upnalab/usarrayheightmod/Paper Photos/All Photos/Array/Foto1.png

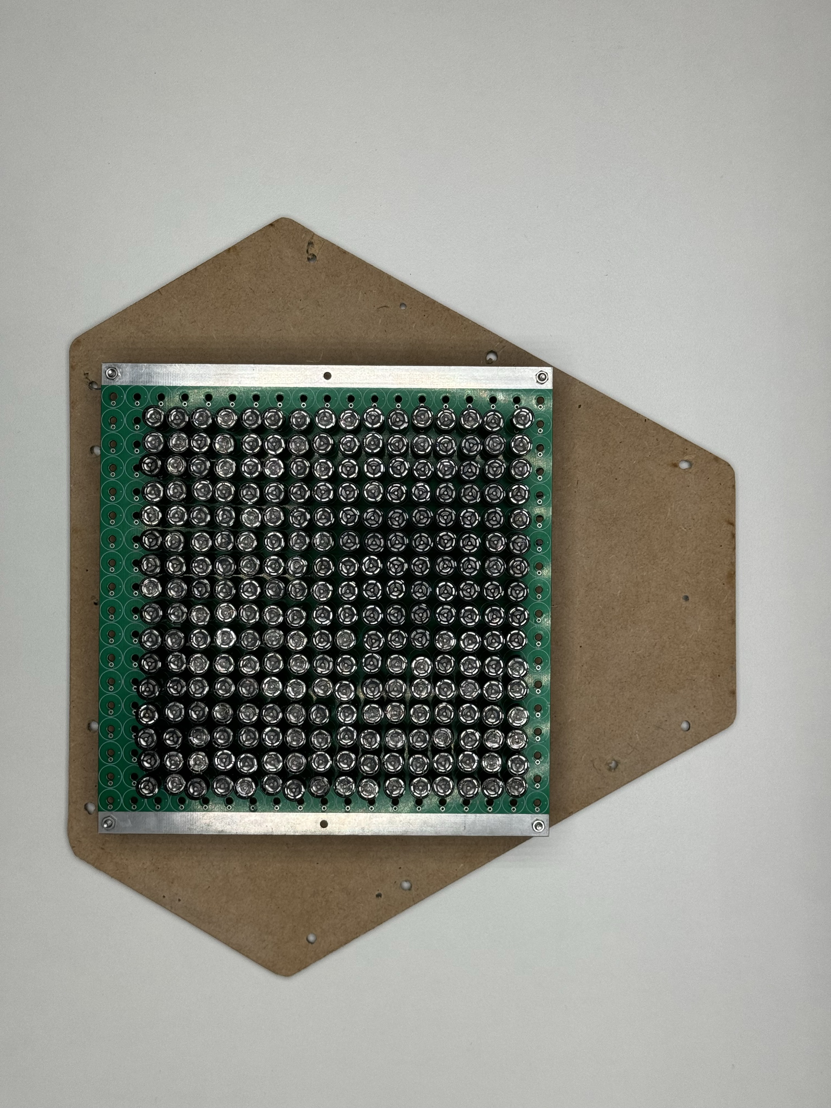
Paper Photos/All Photos/Array/Foto1.png
