upnalab/usarrayheightmod/Paper Photos/All Photos/Array/Foto2.png

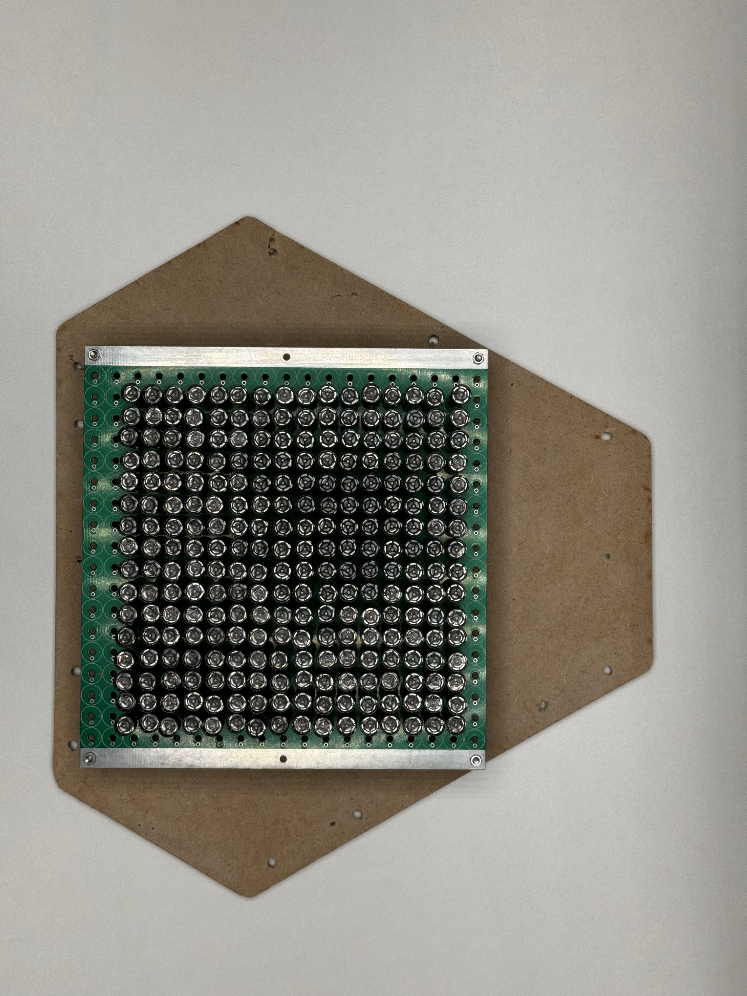
Paper Photos/All Photos/Array/Foto2.png
