upnalab/usarrayheightmod/Paper Photos/All Photos/Array/Foto3.png

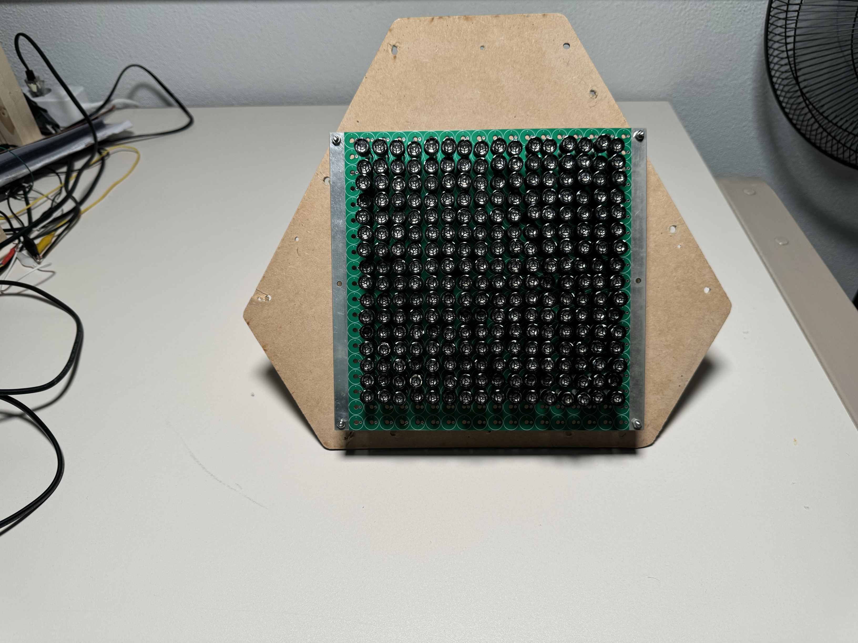
Paper Photos/All Photos/Array/Foto3.png
