upnalab/usarrayheightmod/Paper Photos/All Photos/Array/Foto4.png

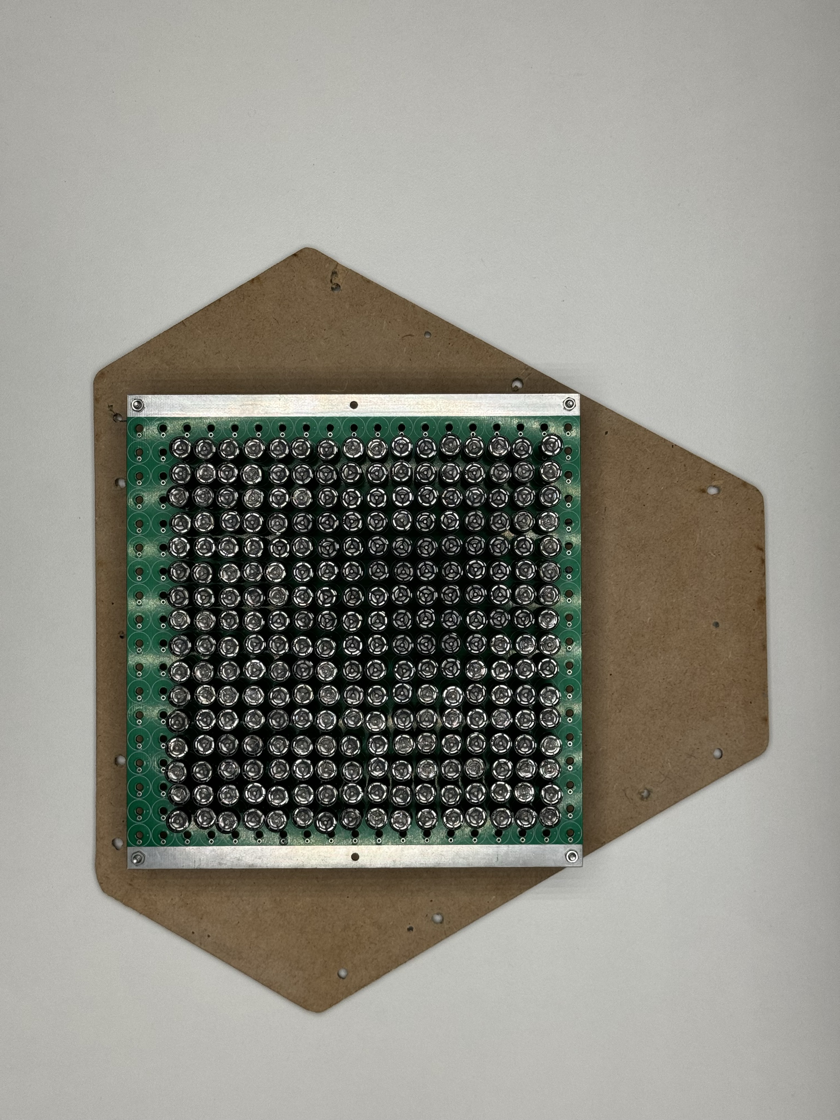
Paper Photos/All Photos/Array/Foto4.png
