upnalab/usarrayheightmod/Paper Photos/All Photos/Array/Foto5.png

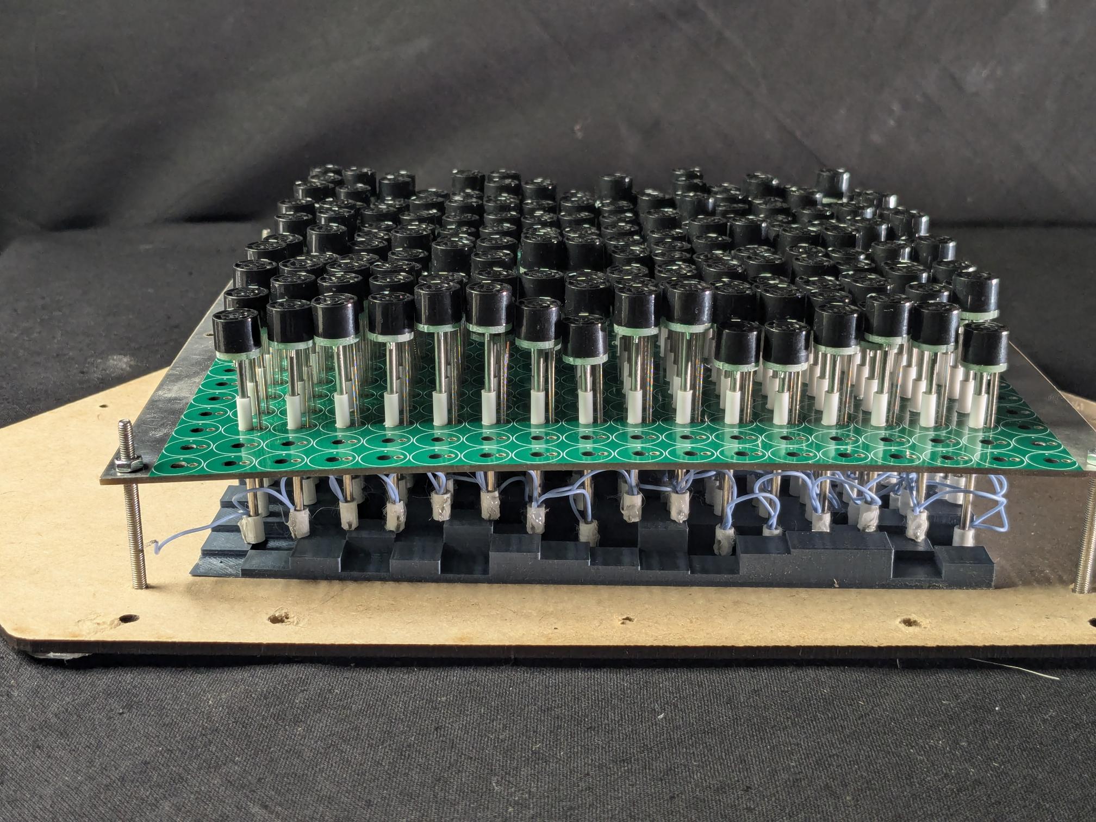
Paper Photos/All Photos/Array/Foto5.png
