upnalab/usarrayheightmod/Paper Photos/All Photos/Array/Foto6.png

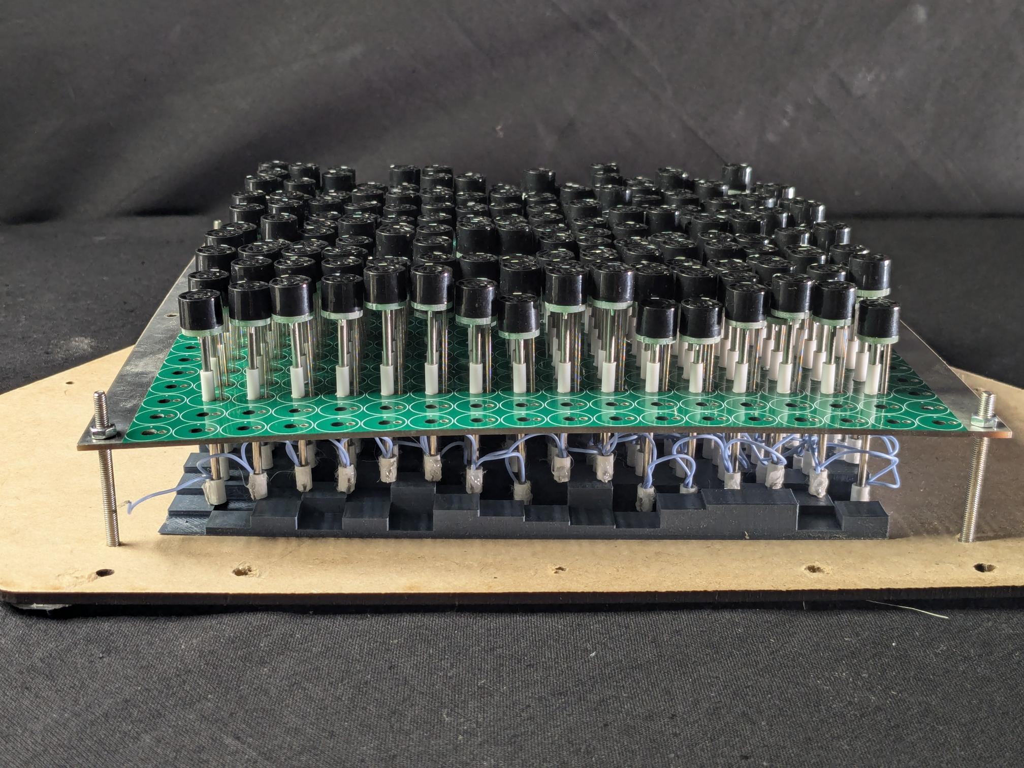
Paper Photos/All Photos/Array/Foto6.png
