upnalab/usarrayheightmod/Paper Photos/All Photos/Array/Foto7.png

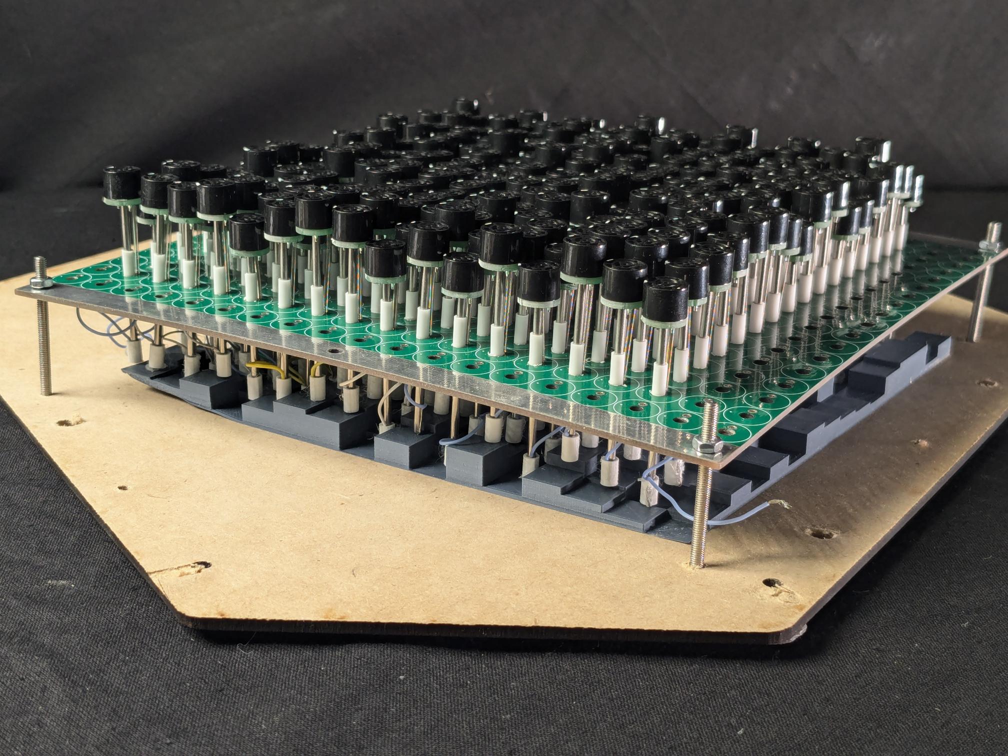
Paper Photos/All Photos/Array/Foto7.png
