upnalab/usarrayheightmod/Paper Photos/All Photos/Array/Foto8.png

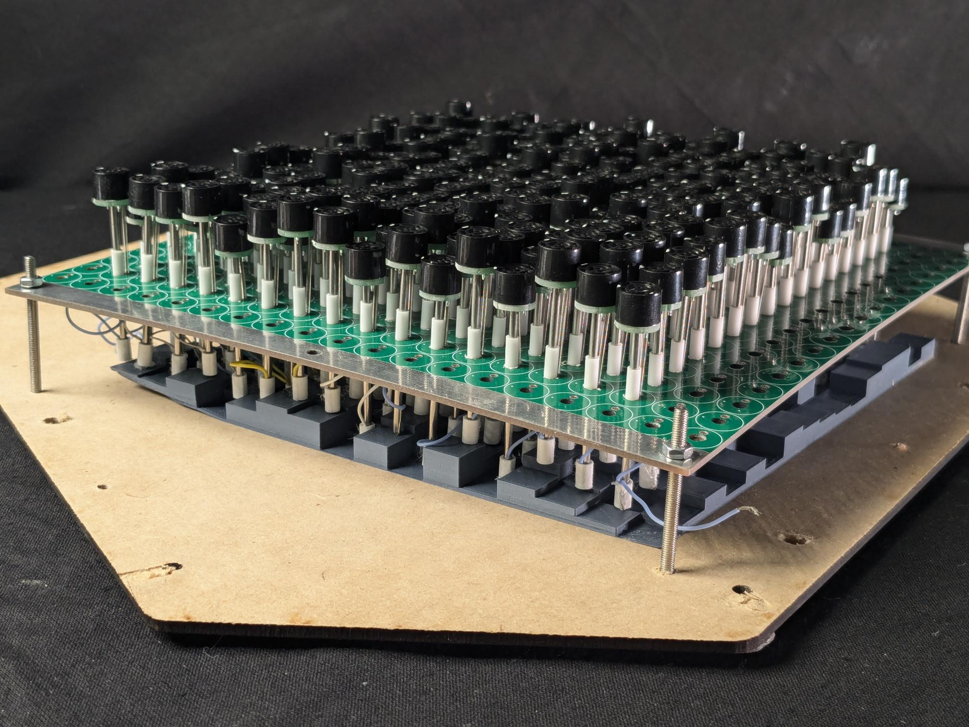
Paper Photos/All Photos/Array/Foto8.png
