upnalab/usarrayheightmod/Paper Photos/All Photos/Array/Foto9.png

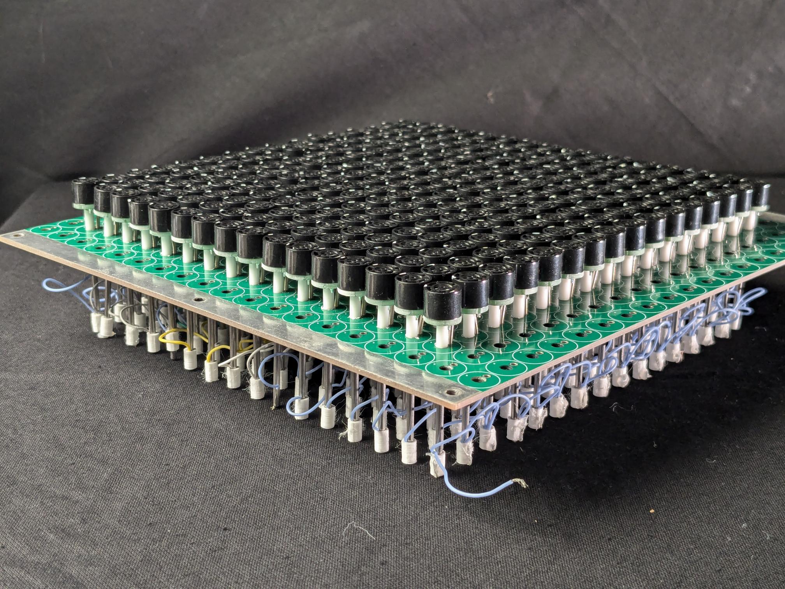
Paper Photos/All Photos/Array/Foto9.png
