upnalab/usarrayheightmod/Paper Photos/All Photos/Array/Foto10.png

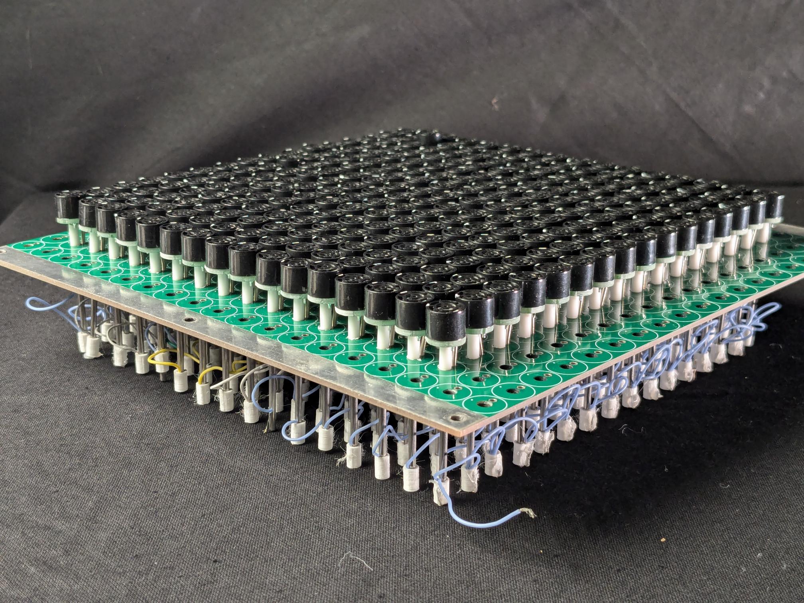
Paper Photos/All Photos/Array/Foto10.png
