upnalab/usarrayheightmod/Paper Photos/All Photos/Array/Foto11.png

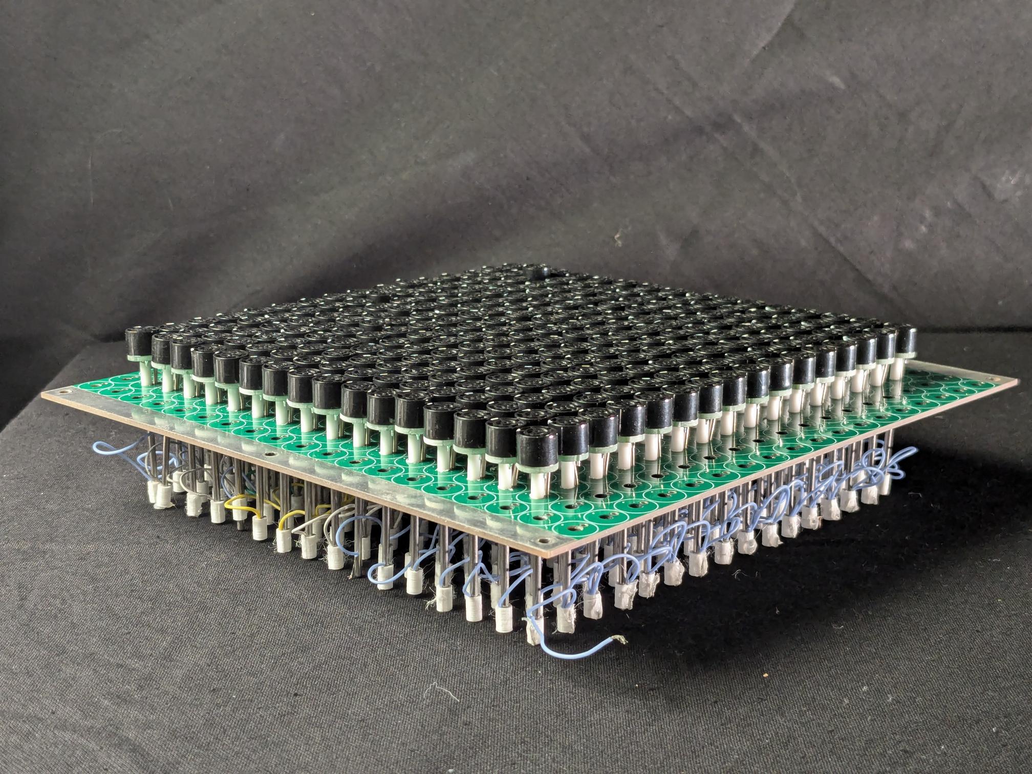
Paper Photos/All Photos/Array/Foto11.png
