upnalab/usarrayheightmod/Paper Photos/All Photos/Array/Foto12.png

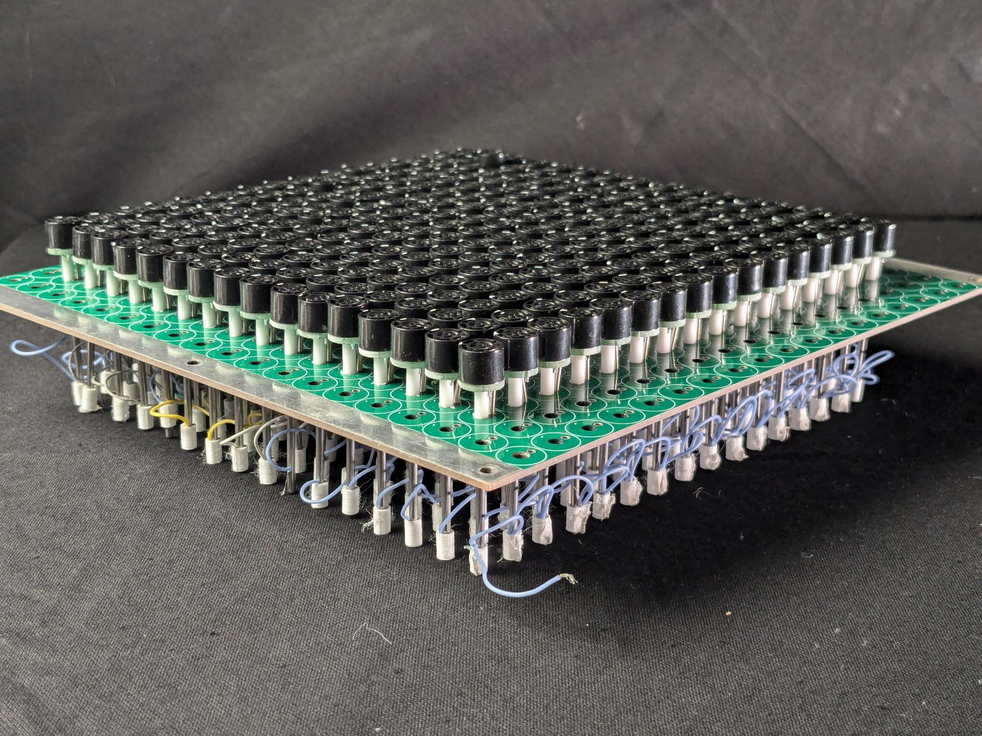
Paper Photos/All Photos/Array/Foto12.png
