upnalab/usarrayheightmod/Paper Photos/All Photos/Array/Foto13.png

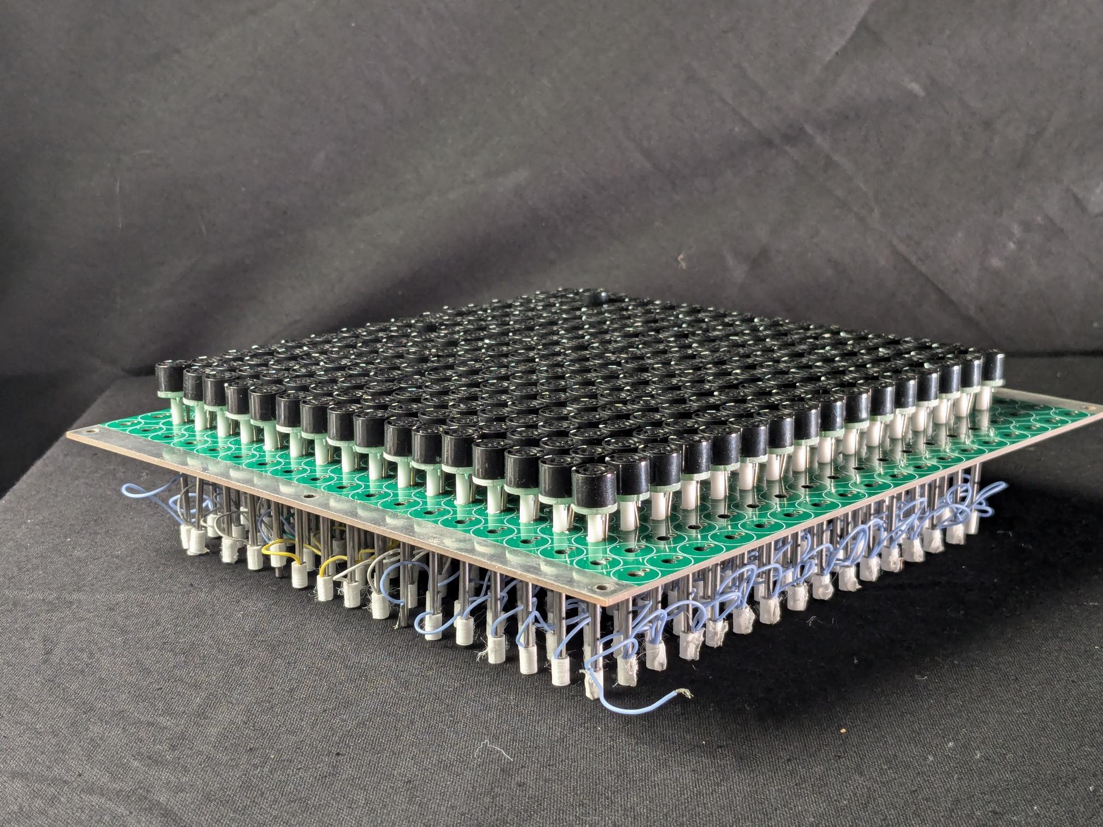
Paper Photos/All Photos/Array/Foto13.png
