upnalab/usarrayheightmod/Paper Photos/All Photos/Array/Foto18.png

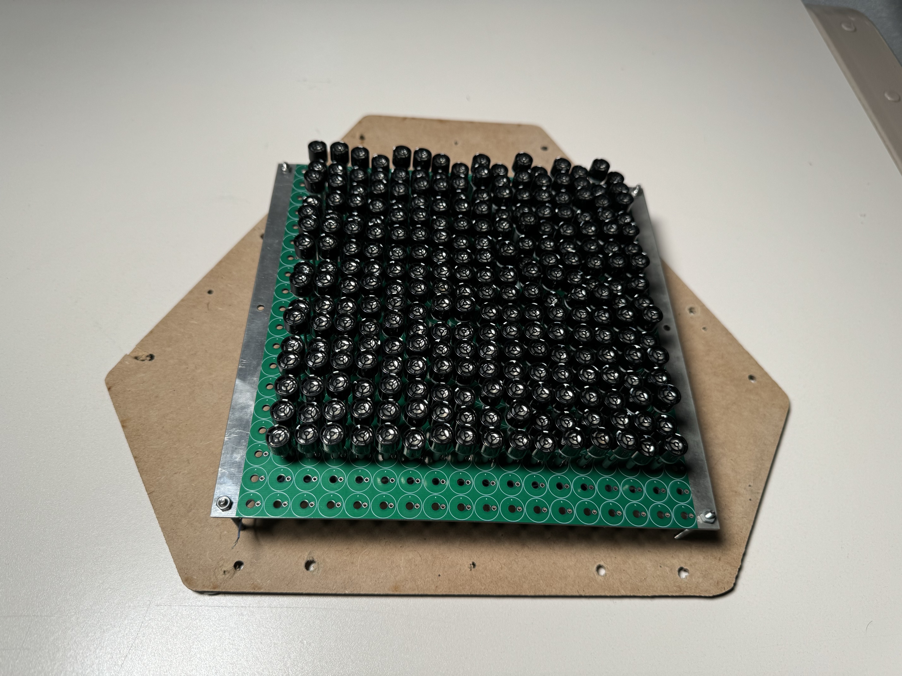
Paper Photos/All Photos/Array/Foto18.png
