upnalab/usarrayheightmod/Paper Photos/All Photos/Array/Foto19.png

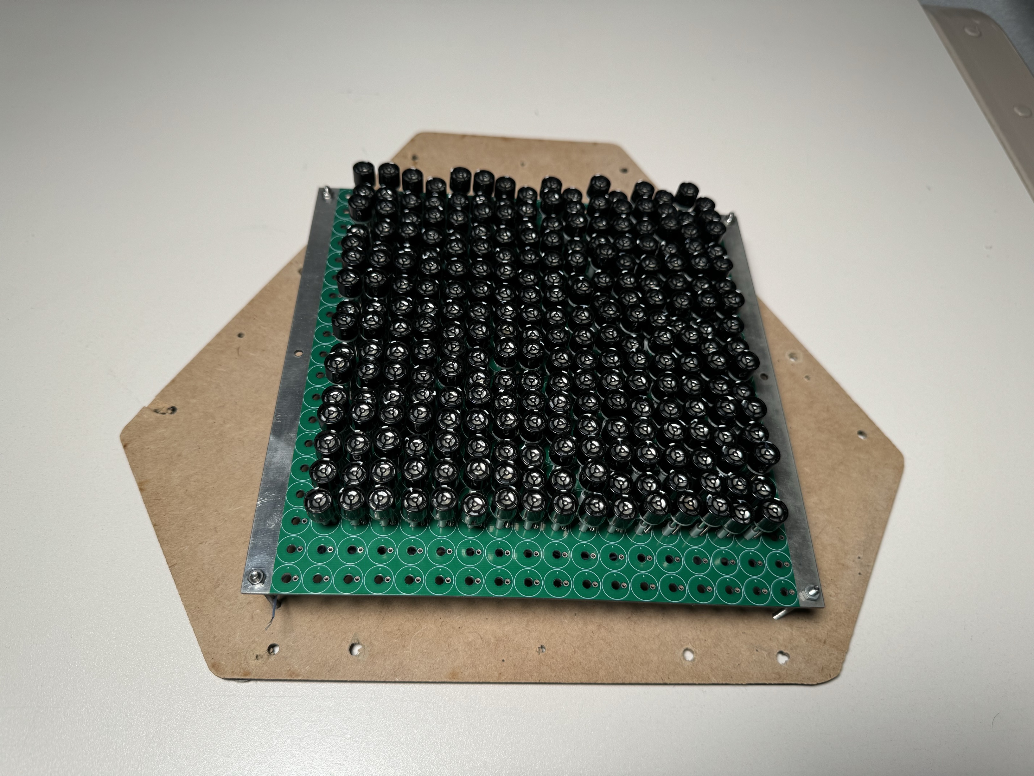
Paper Photos/All Photos/Array/Foto19.png
