upnalab/usarrayheightmod/Paper Photos/All Photos/Array/Foto20.png

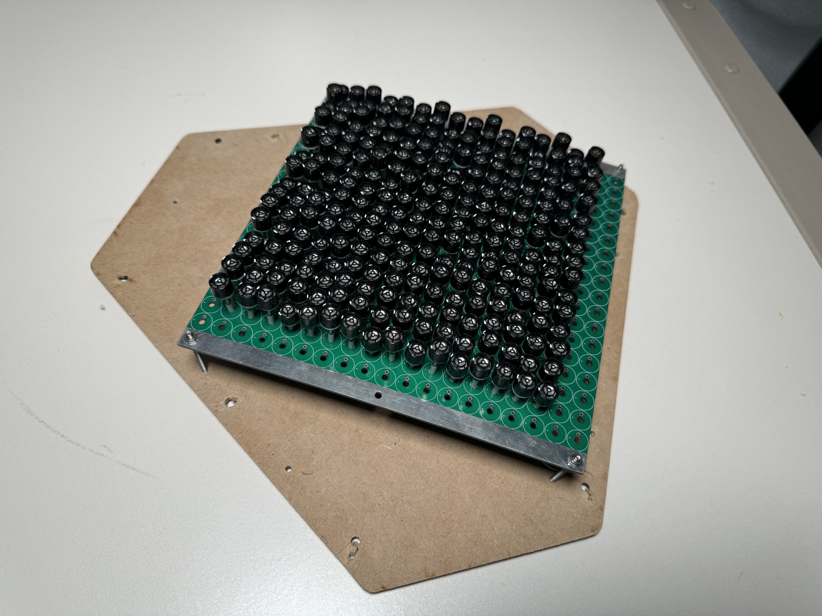
Paper Photos/All Photos/Array/Foto20.png
