upnalab/usarrayheightmod/Paper Photos/All Photos/Array/Foto24.png

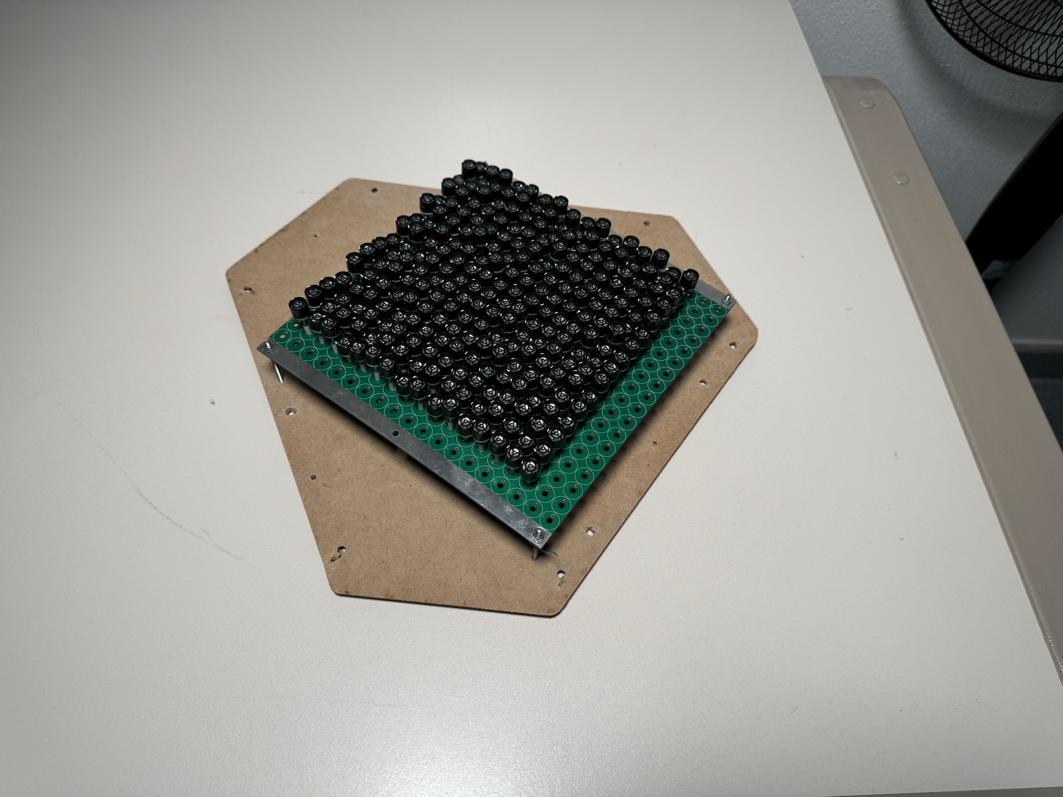
Paper Photos/All Photos/Array/Foto24.png
