upnalab/usarrayheightmod/Paper Photos/All Photos/Array/Foto25.png

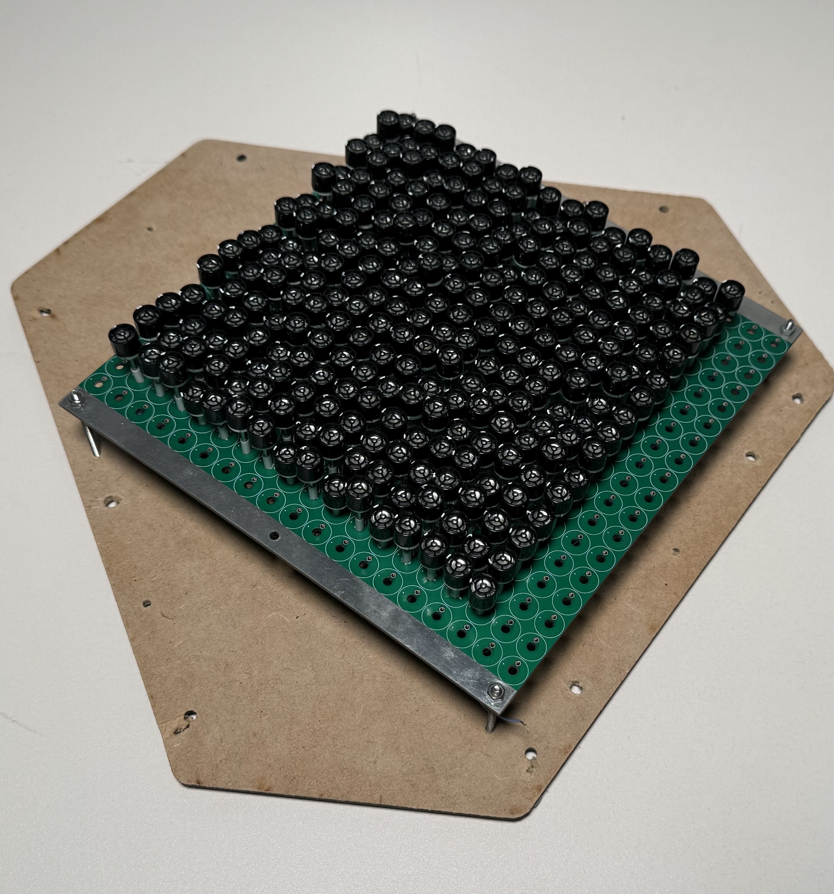
Paper Photos/All Photos/Array/Foto25.png
