upnalab/usarrayheightmod/Paper Photos/All Photos/Array/Foto27.png

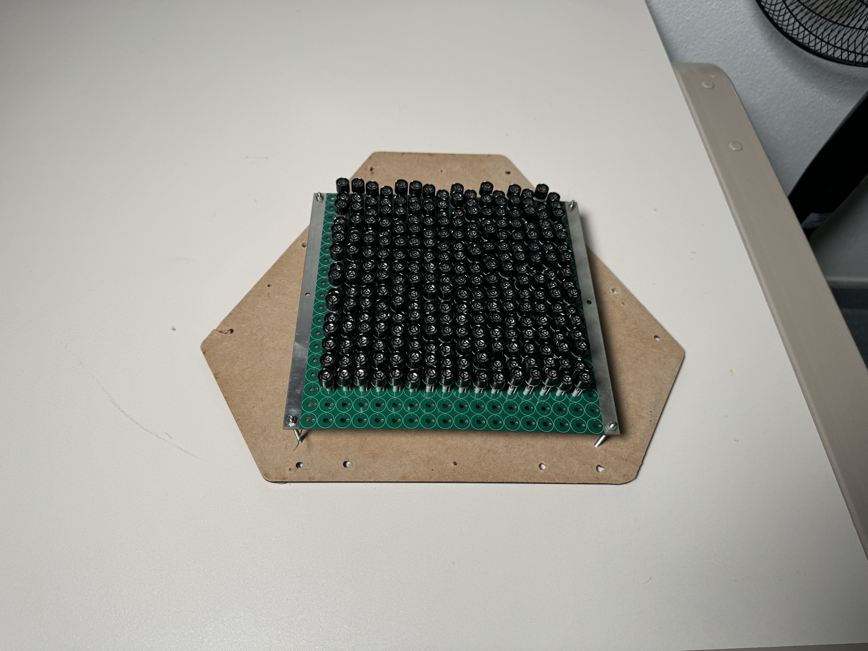
Paper Photos/All Photos/Array/Foto27.png
