upnalab/usarrayheightmod/Paper Photos/All Photos/Array/Foto29.png

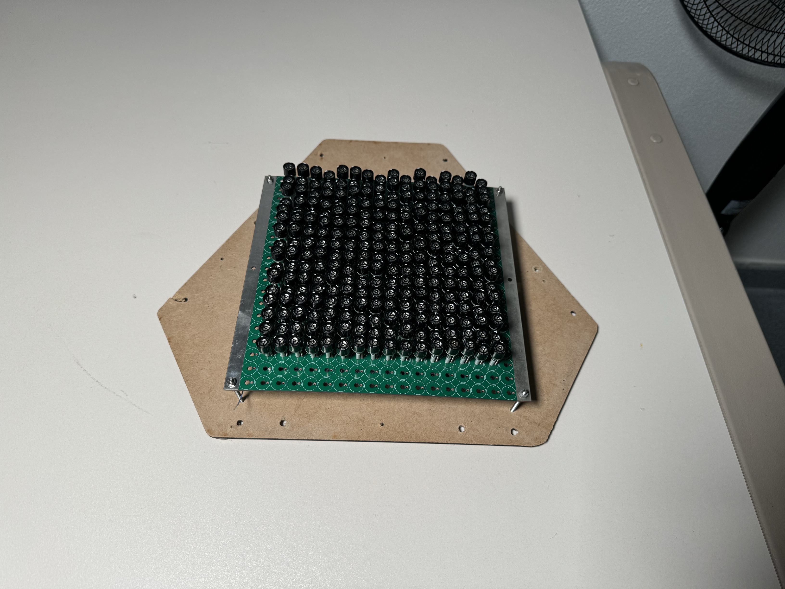
Paper Photos/All Photos/Array/Foto29.png
