upnalab/usarrayheightmod/Paper Photos/All Photos/Array/Foto30.png

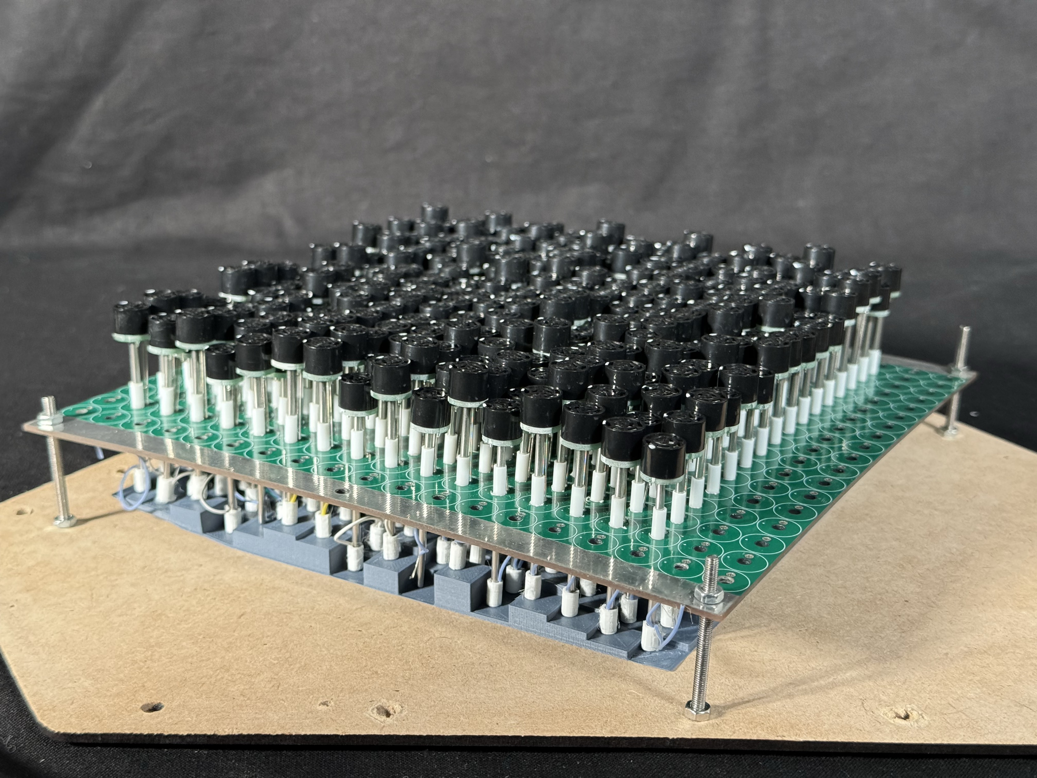
Paper Photos/All Photos/Array/Foto30.png
