upnalab/usarrayheightmod/Paper Photos/All Photos/Array/Foto31.png

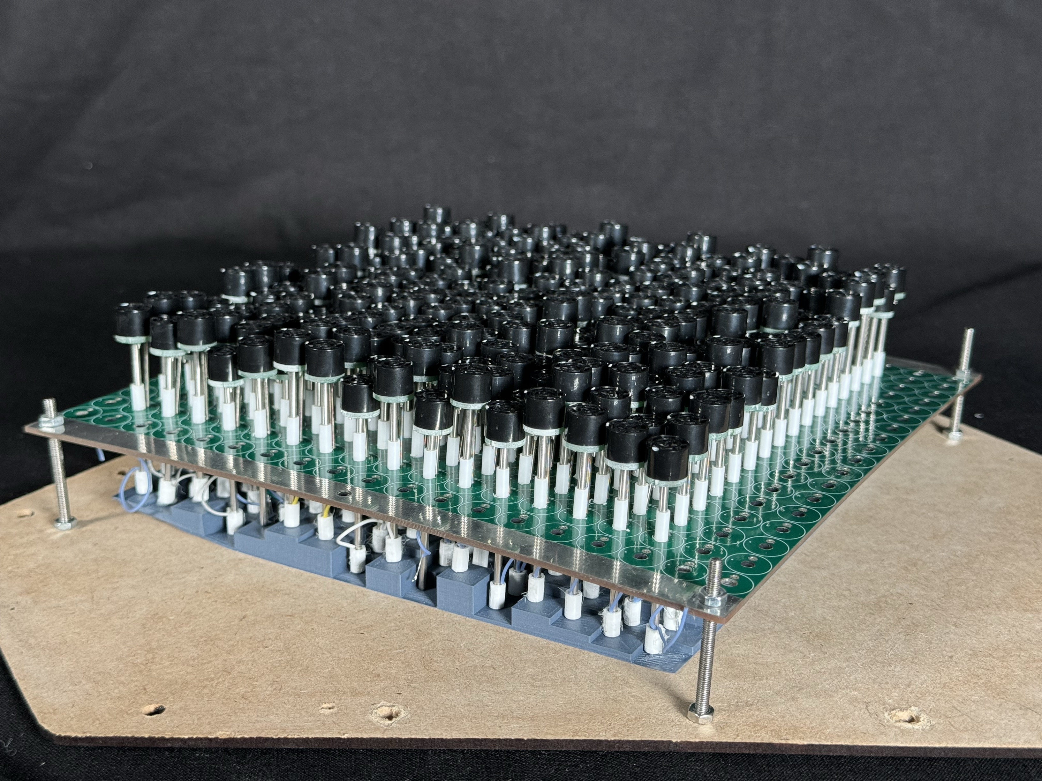
Paper Photos/All Photos/Array/Foto31.png
