upnalab/usarrayheightmod/Paper Photos/All Photos/Array/Foto33.png

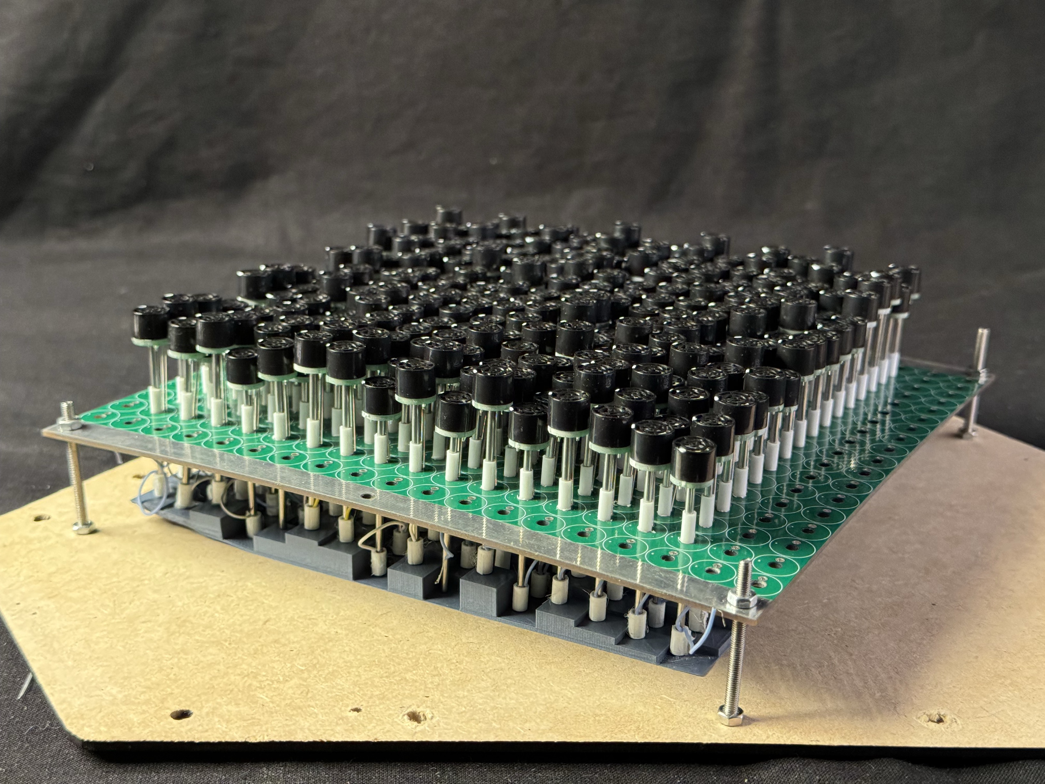
Paper Photos/All Photos/Array/Foto33.png
