upnalab/usarrayheightmod/Paper Photos/All Photos/Array/Foto35.png

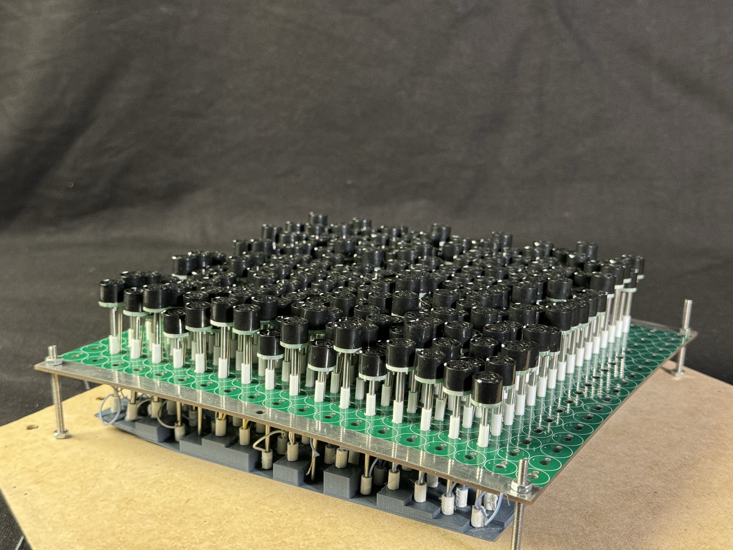
Paper Photos/All Photos/Array/Foto35.png
