upnalab/usarrayheightmod/Paper Photos/All Photos/Array/Foto37.png

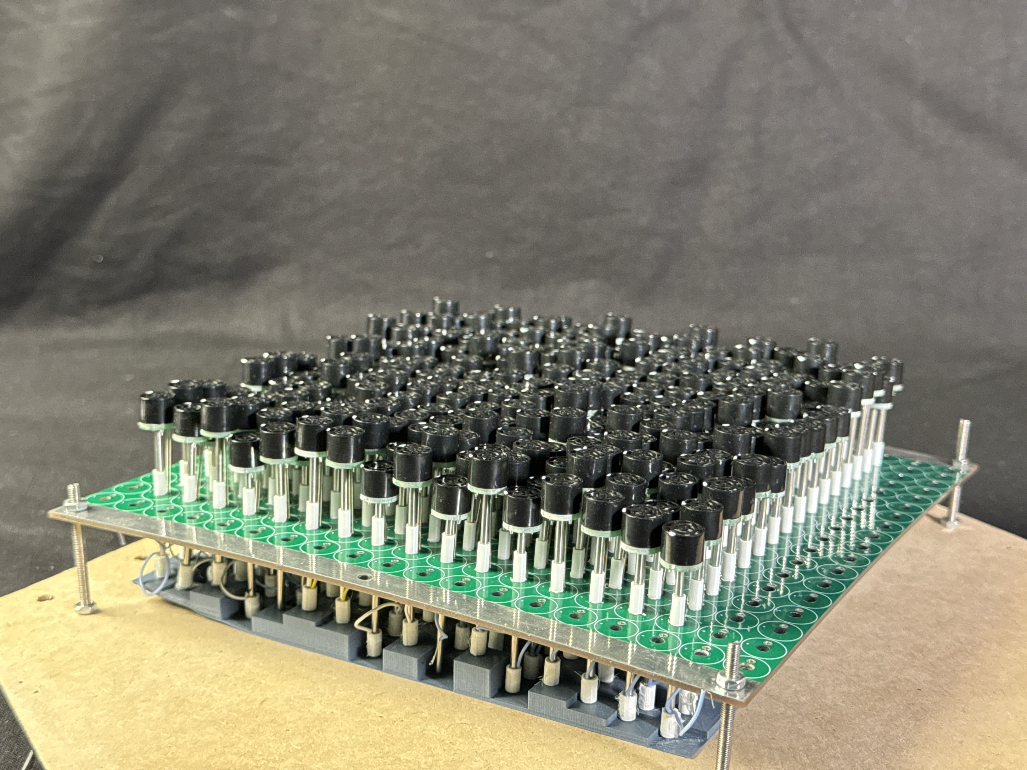
Paper Photos/All Photos/Array/Foto37.png
