upnalab/usarrayheightmod/Paper Photos/All Photos/Array/Foto41.png

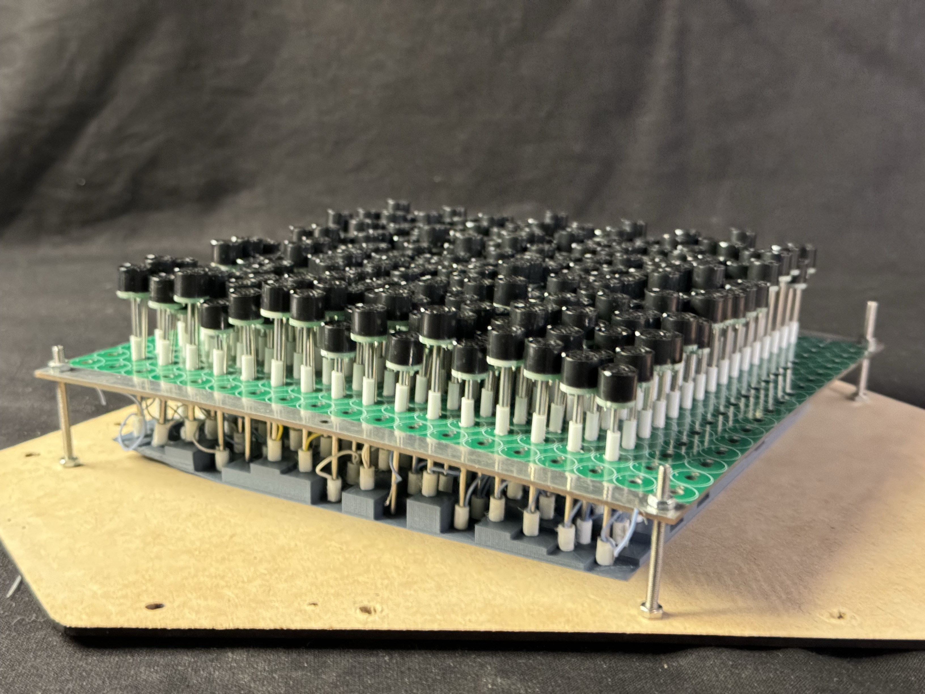
Paper Photos/All Photos/Array/Foto41.png
