upnalab/usarrayheightmod/Paper Photos/All Photos/Array/Foto42.png

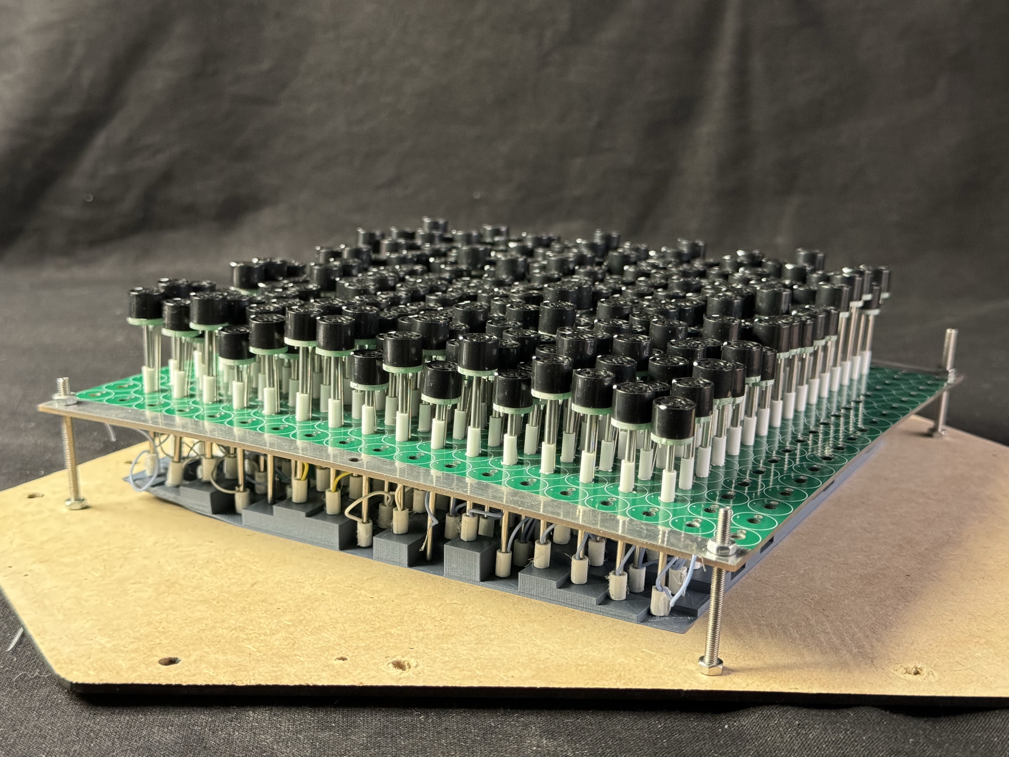
Paper Photos/All Photos/Array/Foto42.png
