upnalab/usarrayheightmod/Paper Photos/All Photos/Array/Foto43.png

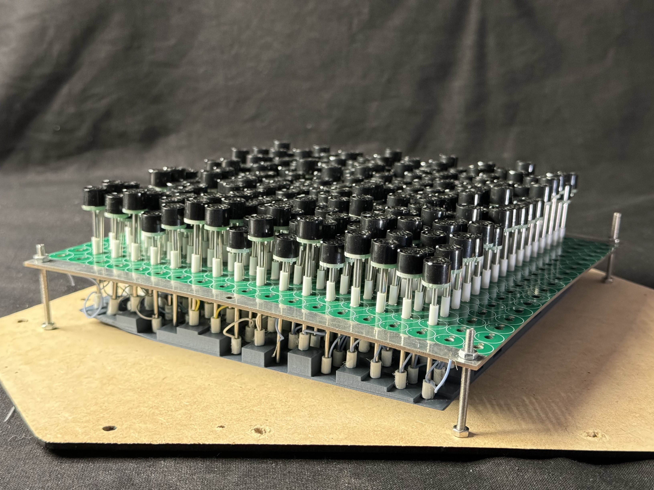
Paper Photos/All Photos/Array/Foto43.png
