upnalab/usarrayheightmod/Paper Photos/All Photos/Array/Foto45.png

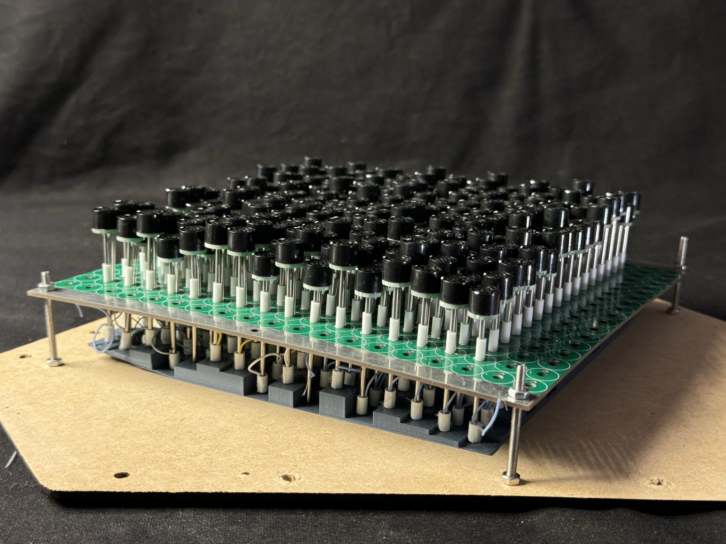
Paper Photos/All Photos/Array/Foto45.png
