upnalab/usarrayheightmod/Paper Photos/All Photos/Array/Foto47.png

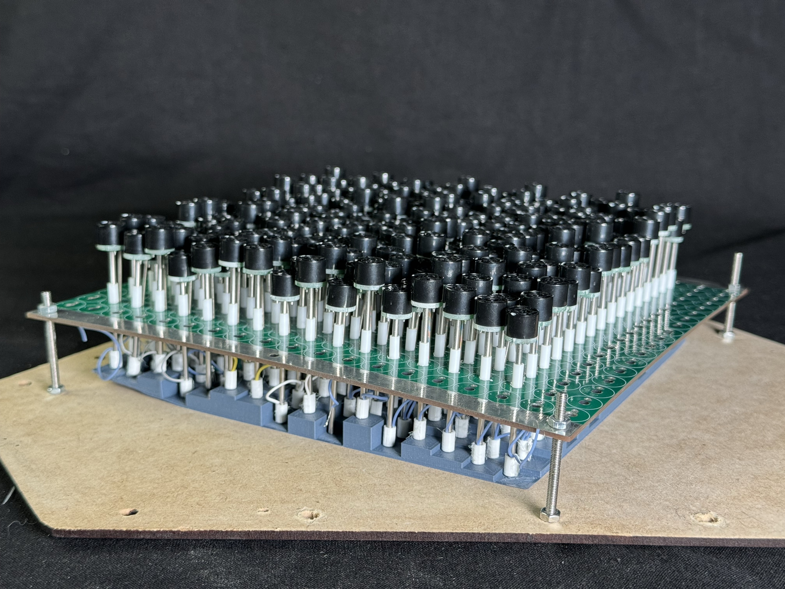
Paper Photos/All Photos/Array/Foto47.png
