upnalab/usarrayheightmod/Paper Photos/All Photos/Array/Foto49.png

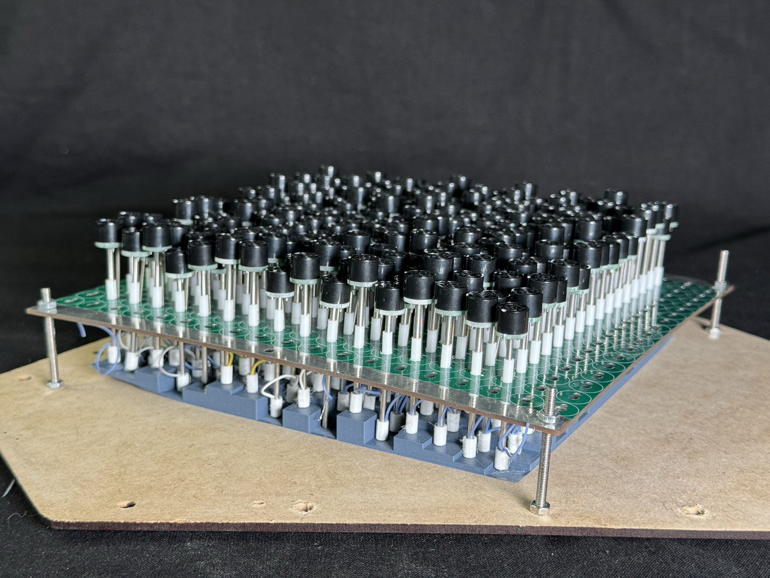
Paper Photos/All Photos/Array/Foto49.png
