upnalab/usarrayheightmod/Paper Photos/All Photos/Array/Foto51.png

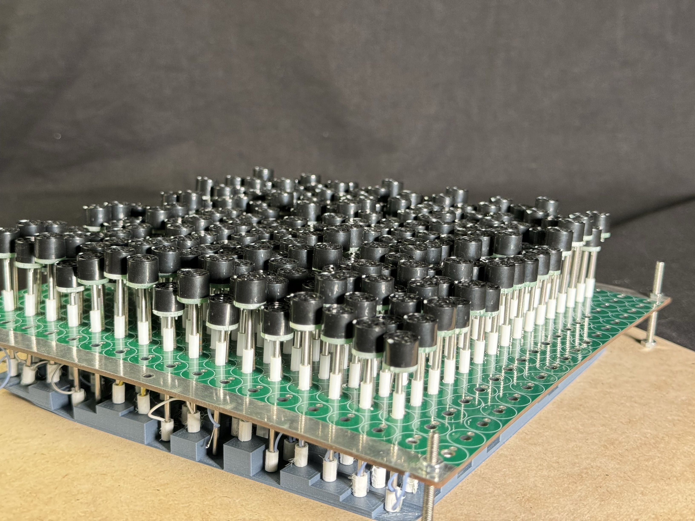
Paper Photos/All Photos/Array/Foto51.png
