upnalab/usarrayheightmod/Paper Photos/All Photos/Array/Foto52.png

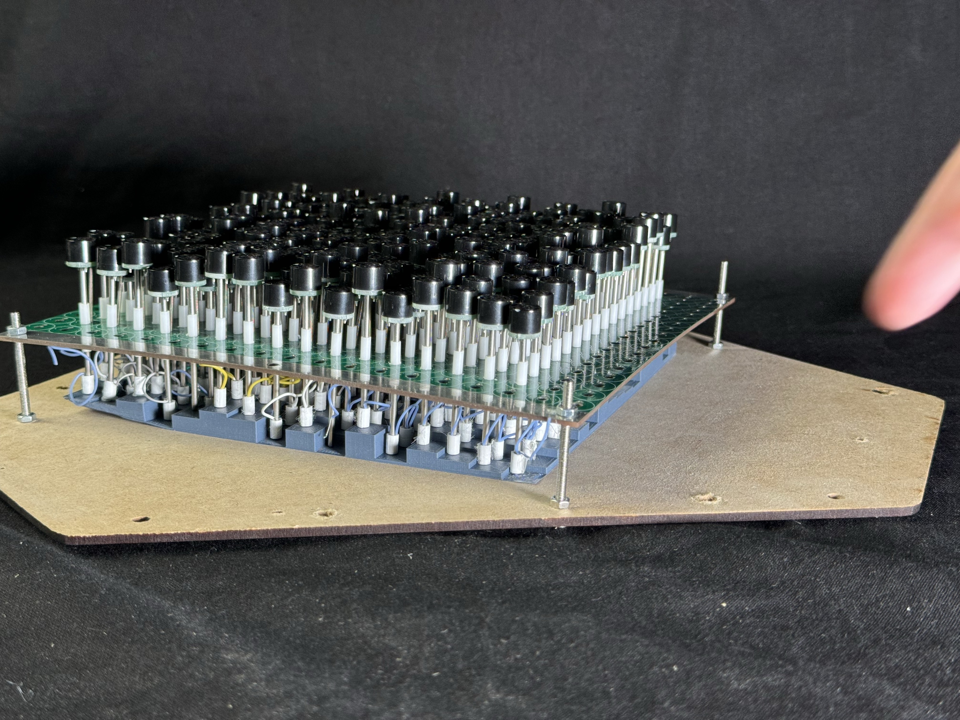
Paper Photos/All Photos/Array/Foto52.png
