upnalab/usarrayheightmod/Paper Photos/All Photos/Array/Foto53.png

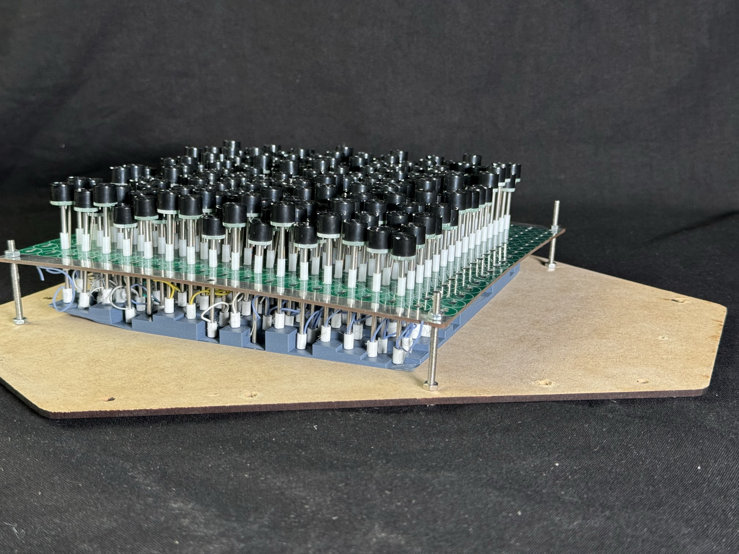
Paper Photos/All Photos/Array/Foto53.png
