upnalab/usarrayheightmod/Paper Photos/All Photos/Array/Foto54.png

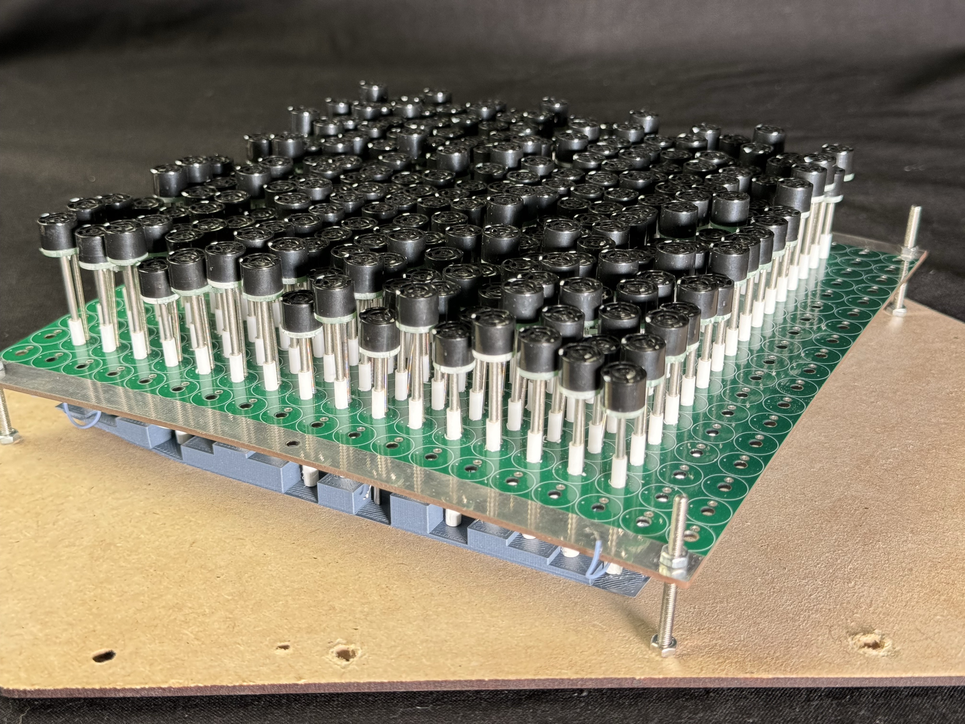
Paper Photos/All Photos/Array/Foto54.png
