upnalab/usarrayheightmod/Paper Photos/All Photos/Array/Foto57.png

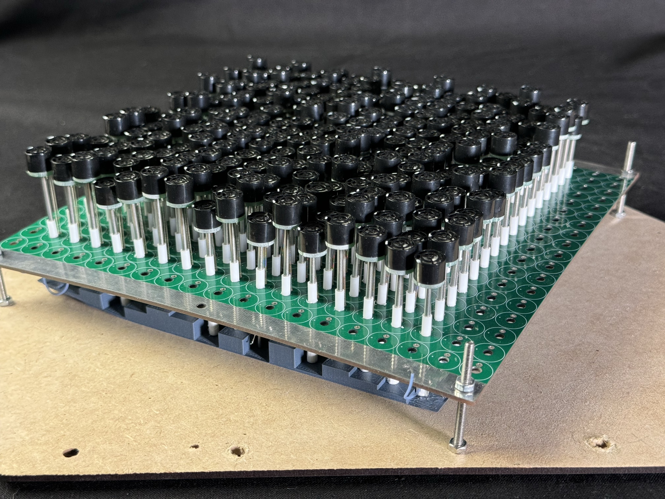
Paper Photos/All Photos/Array/Foto57.png
