upnalab/usarrayheightmod/Paper Photos/All Photos/Array/Foto58.png

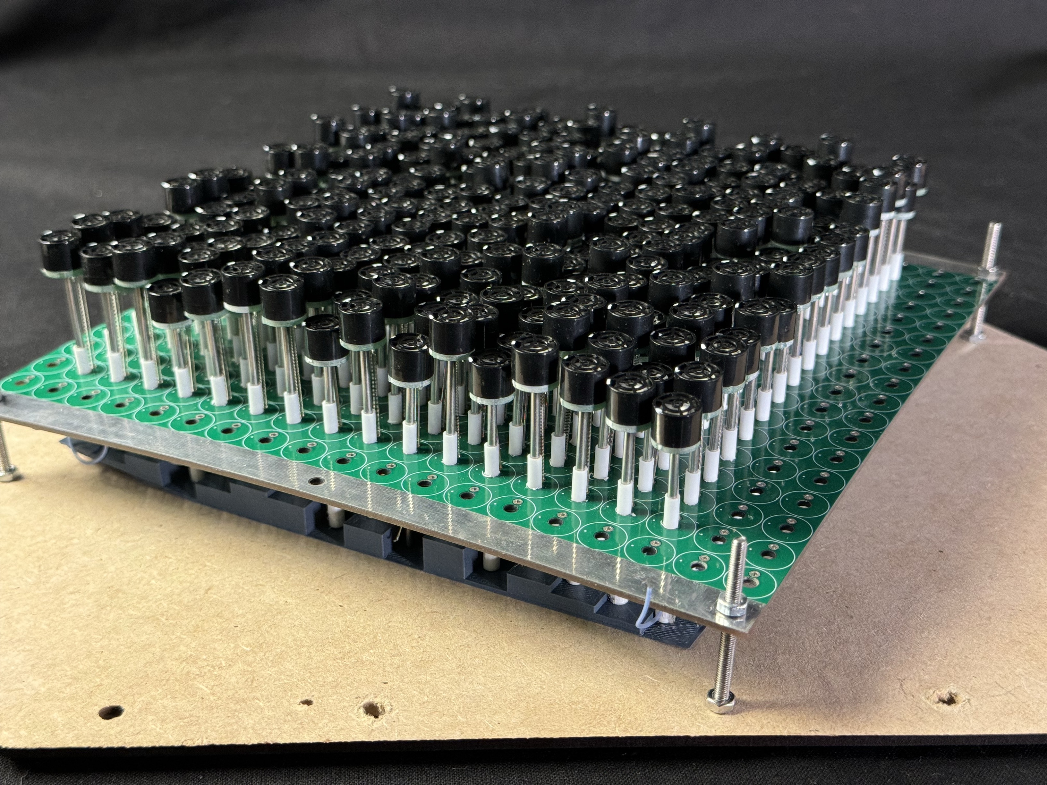
Paper Photos/All Photos/Array/Foto58.png
