upnalab/usarrayheightmod/Paper Photos/All Photos/Array/Foto60.png

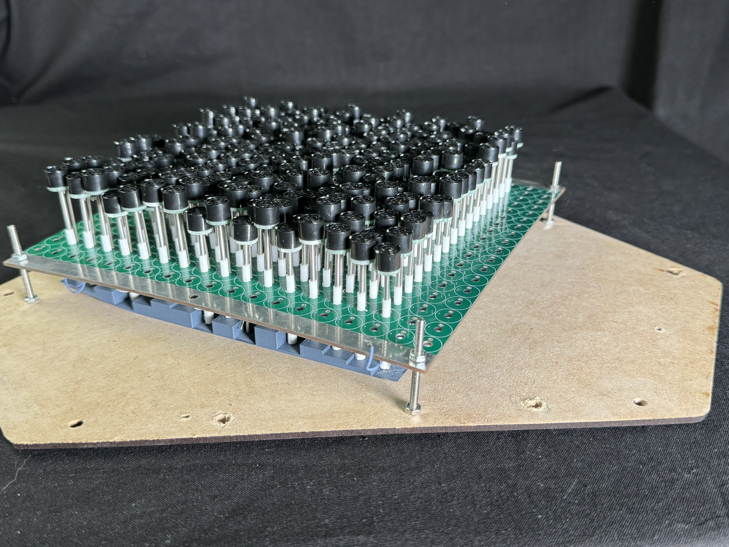
Paper Photos/All Photos/Array/Foto60.png
