upnalab/usarrayheightmod/Paper Photos/All Photos/Array/Foto63.png

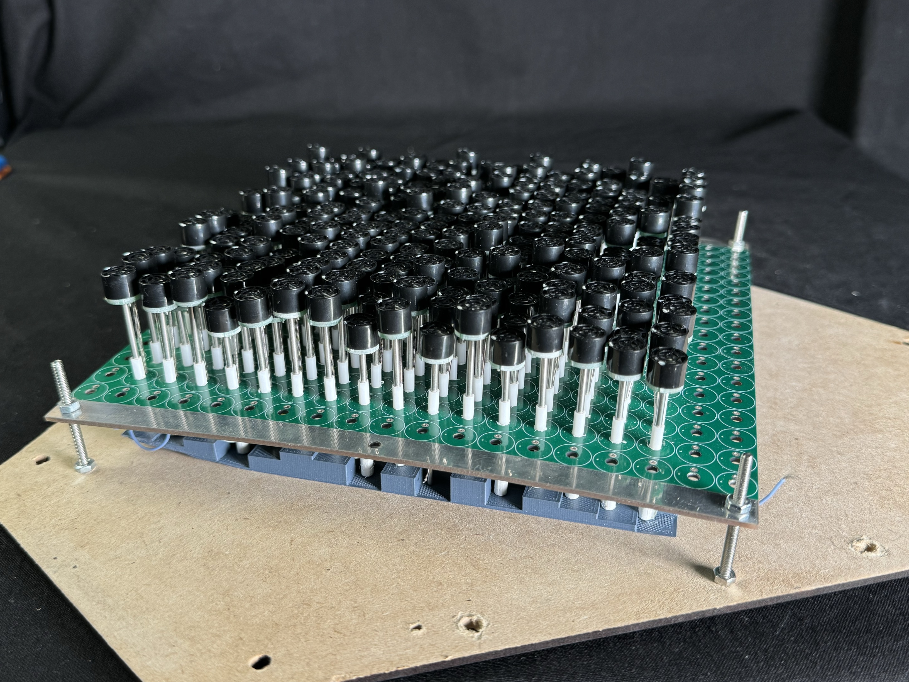
Paper Photos/All Photos/Array/Foto63.png
