upnalab/usarrayheightmod/Paper Photos/All Photos/Array/Foto64.png

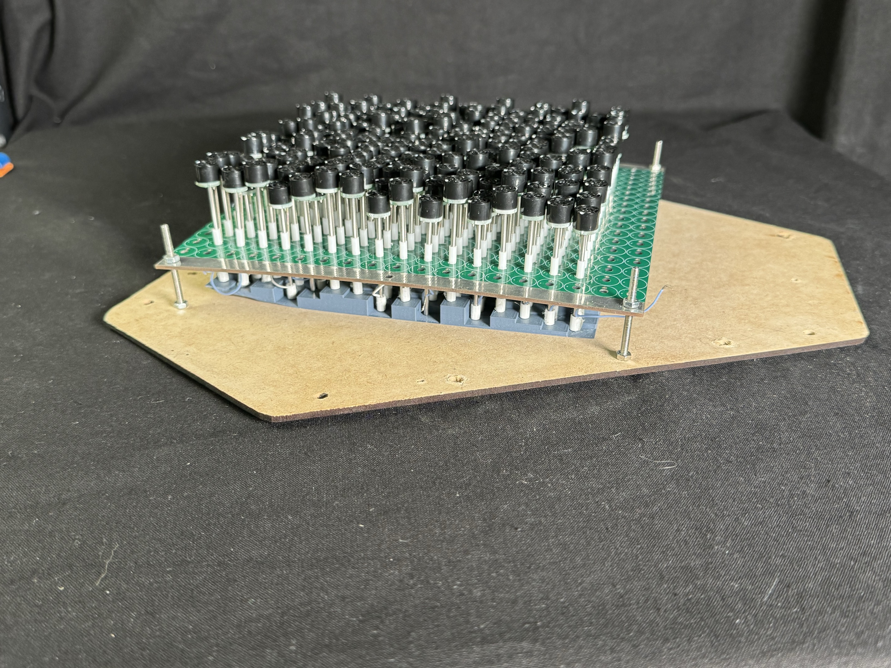
Paper Photos/All Photos/Array/Foto64.png
