upnalab/usarrayheightmod/Paper Photos/All Photos/Array/Foto67.png

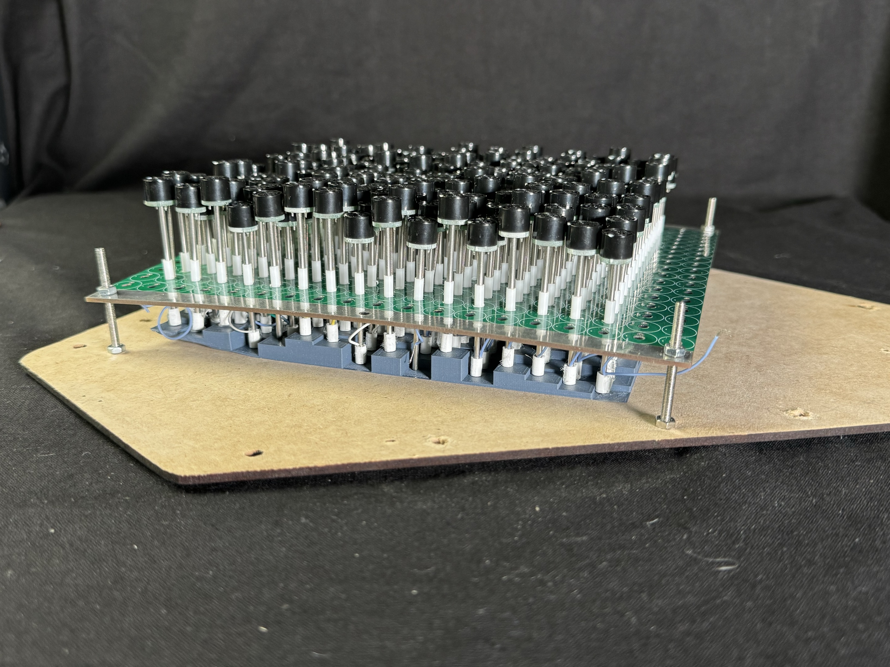
Paper Photos/All Photos/Array/Foto67.png
