upnalab/usarrayheightmod/Paper Photos/All Photos/Array/Foto68.png

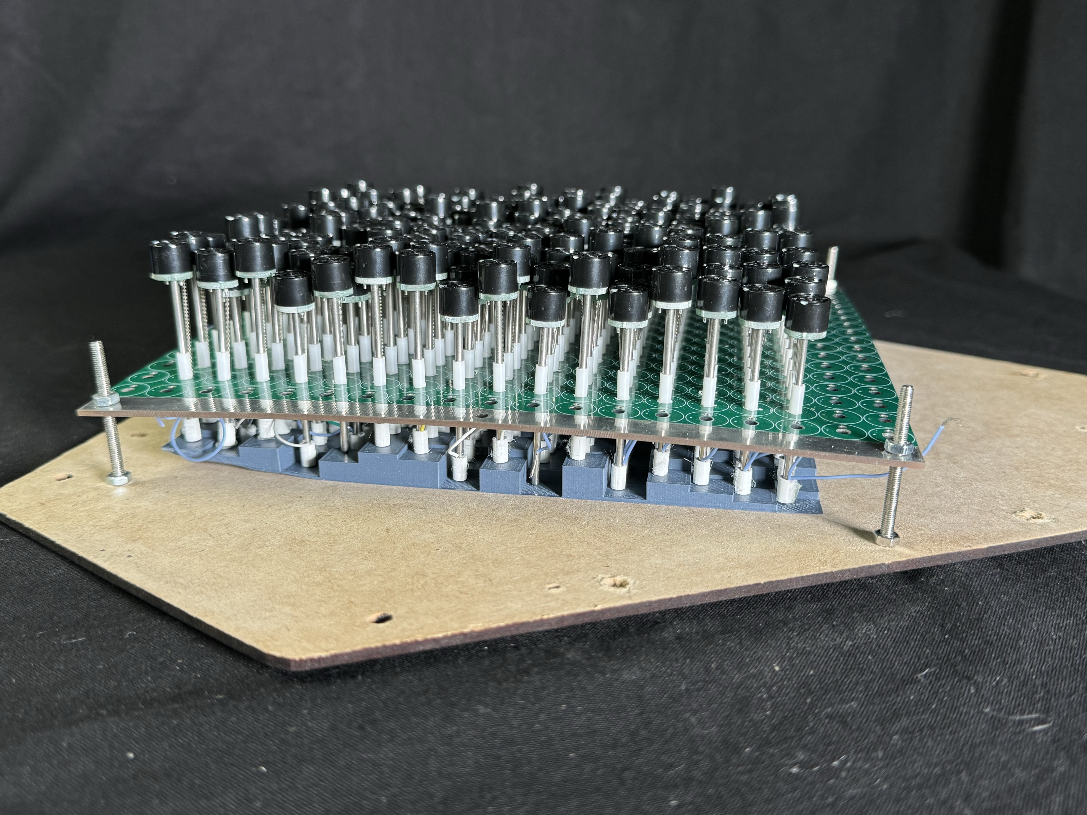
Paper Photos/All Photos/Array/Foto68.png
