upnalab/usarrayheightmod/Paper Photos/All Photos/Metasurface/Foto1.png

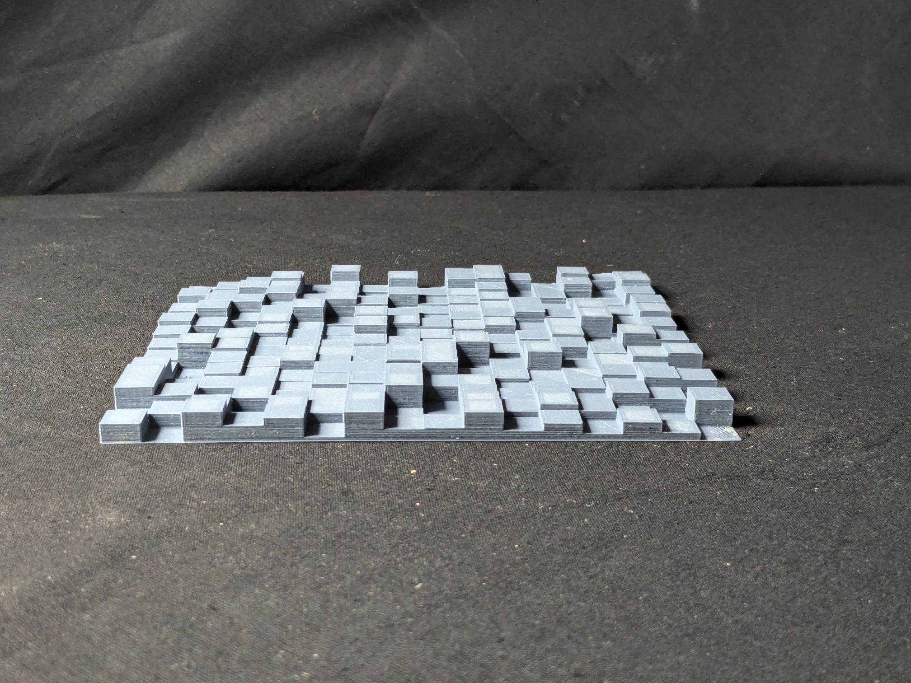
Paper Photos/All Photos/Metasurface/Foto1.png
