upnalab/usarrayheightmod/Paper Photos/All Photos/Metasurface/Foto3.png

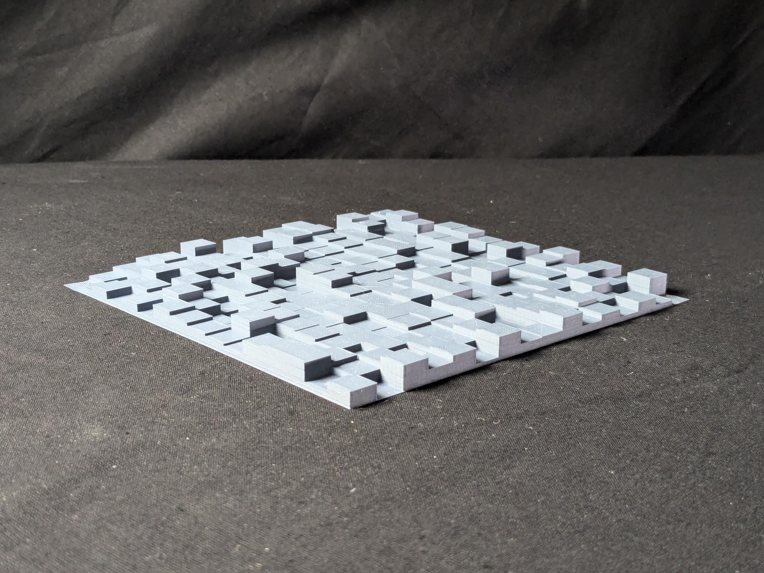
Paper Photos/All Photos/Metasurface/Foto3.png
