upnalab/usarrayheightmod/Paper Photos/All Photos/Scan_SetUp/_DSC2678.JPG

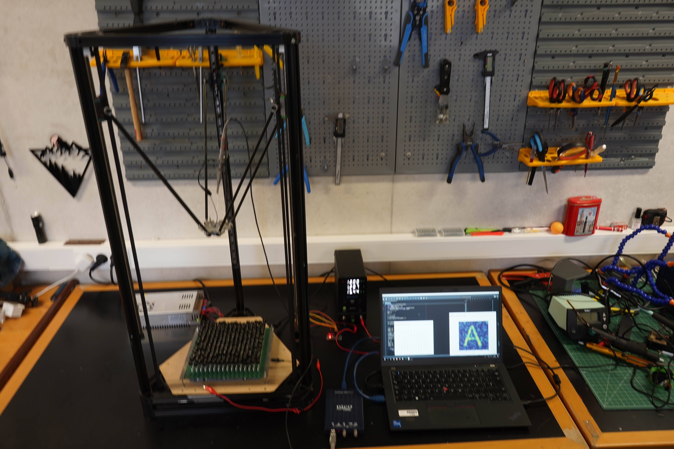
Paper Photos/All Photos/Scan_SetUp/_DSC2678.JPG
