upnalab/usarrayheightmod/Paper Photos/All Photos/Scan_SetUp/_DSC2679.JPG

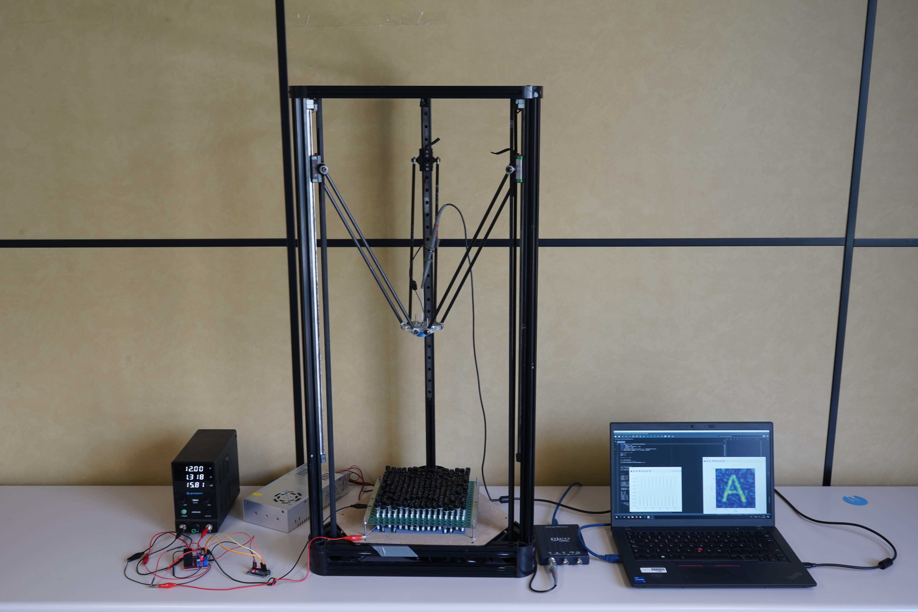
Paper Photos/All Photos/Scan_SetUp/_DSC2679.JPG
