upnalab/usarrayheightmod/Paper Photos/Figure2.png

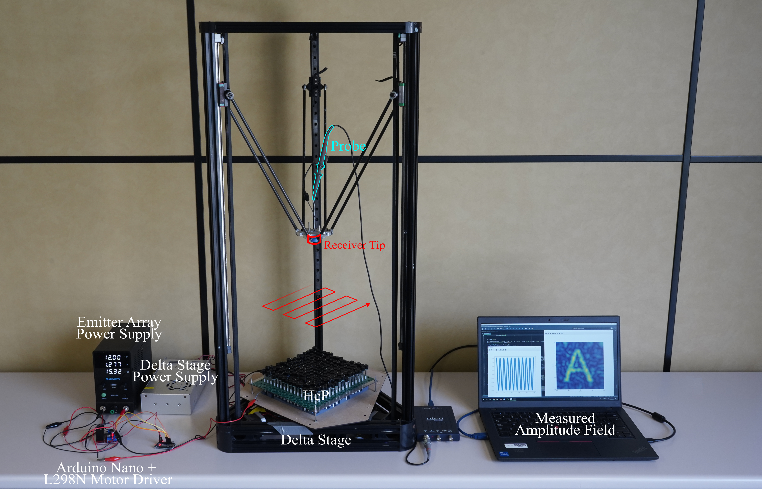
Paper Photos/Figure2.png
