upnalab/usarrayheightmod/patterns/12.png

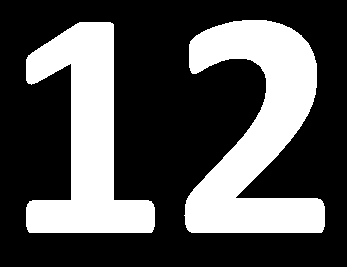
patterns/12.png
