upnalab/usarrayheightmod/patterns/A.png

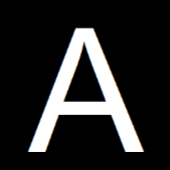
patterns/A.png
