upnalab/usarrayheightmod/patterns/star.png

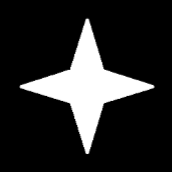
patterns/star.png
