upnalab/usarrayheightmod/measurements/experHeightMod_12.png

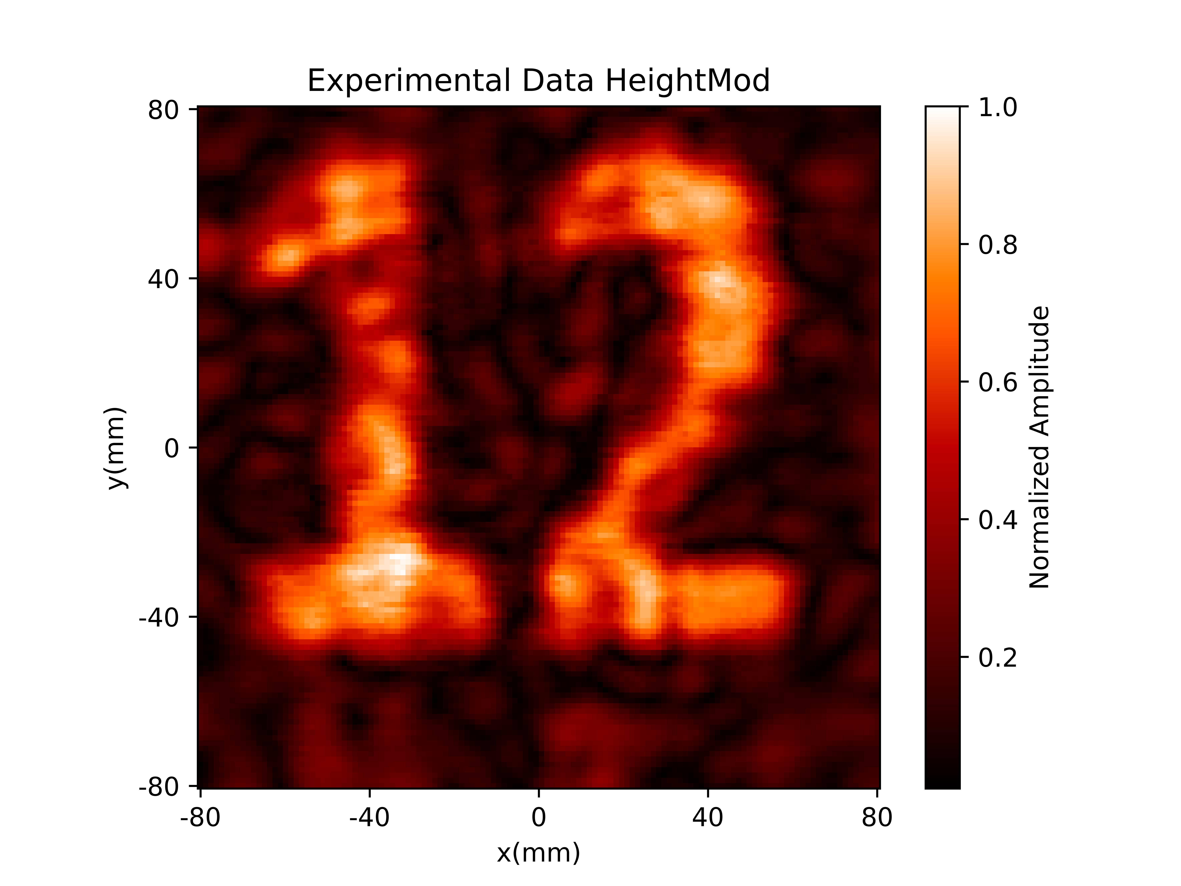
measurements/experHeightMod_12.png
