upnalab/usarrayheightmod/measurements/experHeightMod_A.png

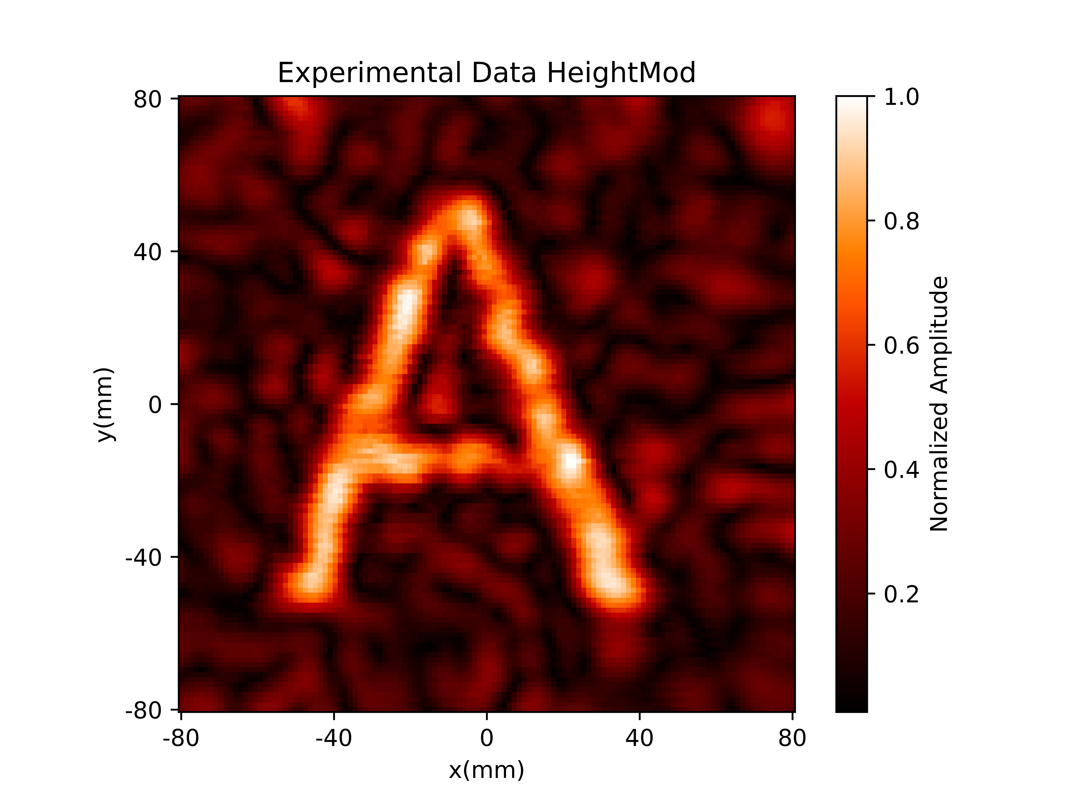
measurements/experHeightMod_A.png
