upnalab/usarrayheightmod/measurements/experHeightMod_star.png

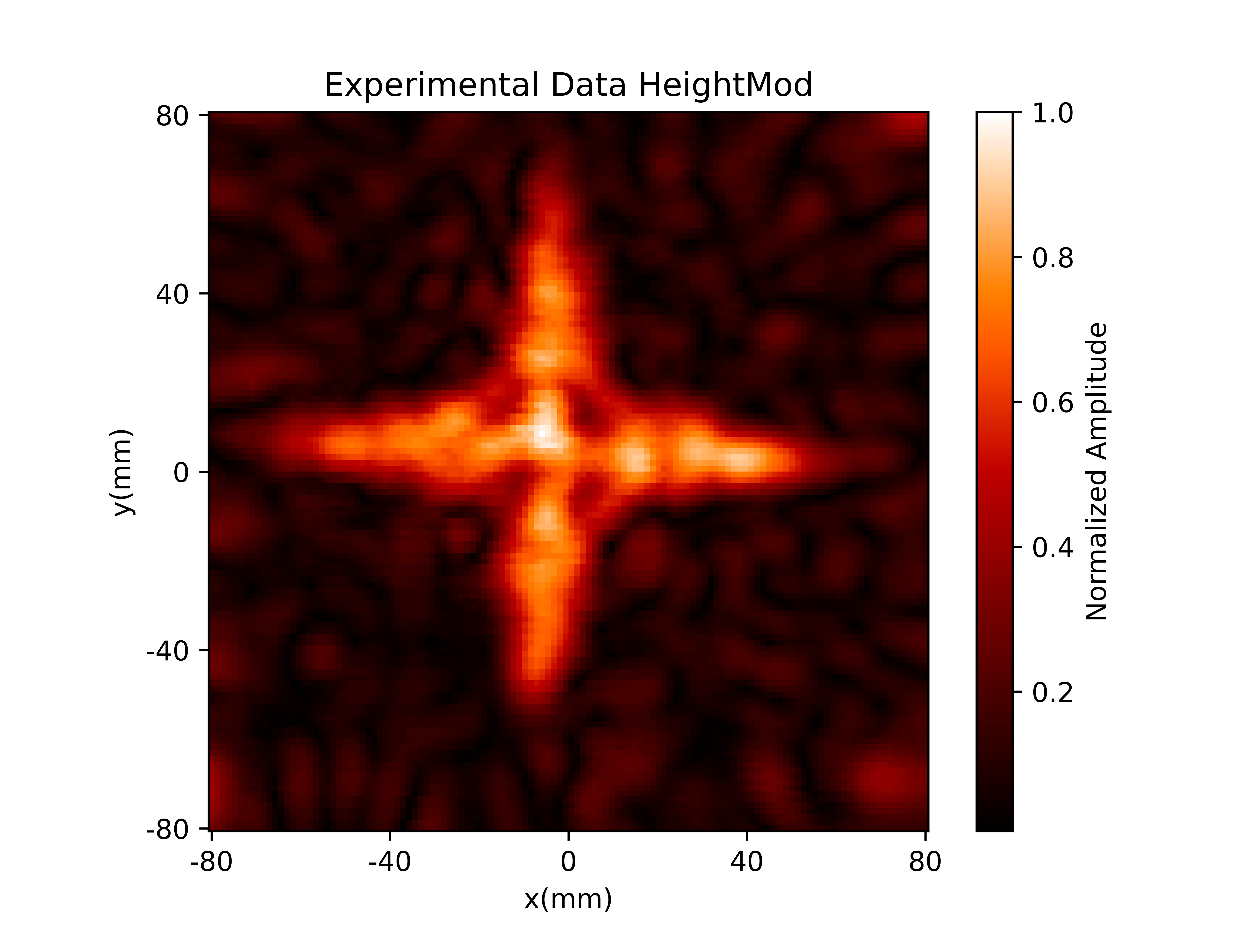
measurements/experHeightMod_star.png
