upnalab/usarrayheightmod/measurements/sim_12.png

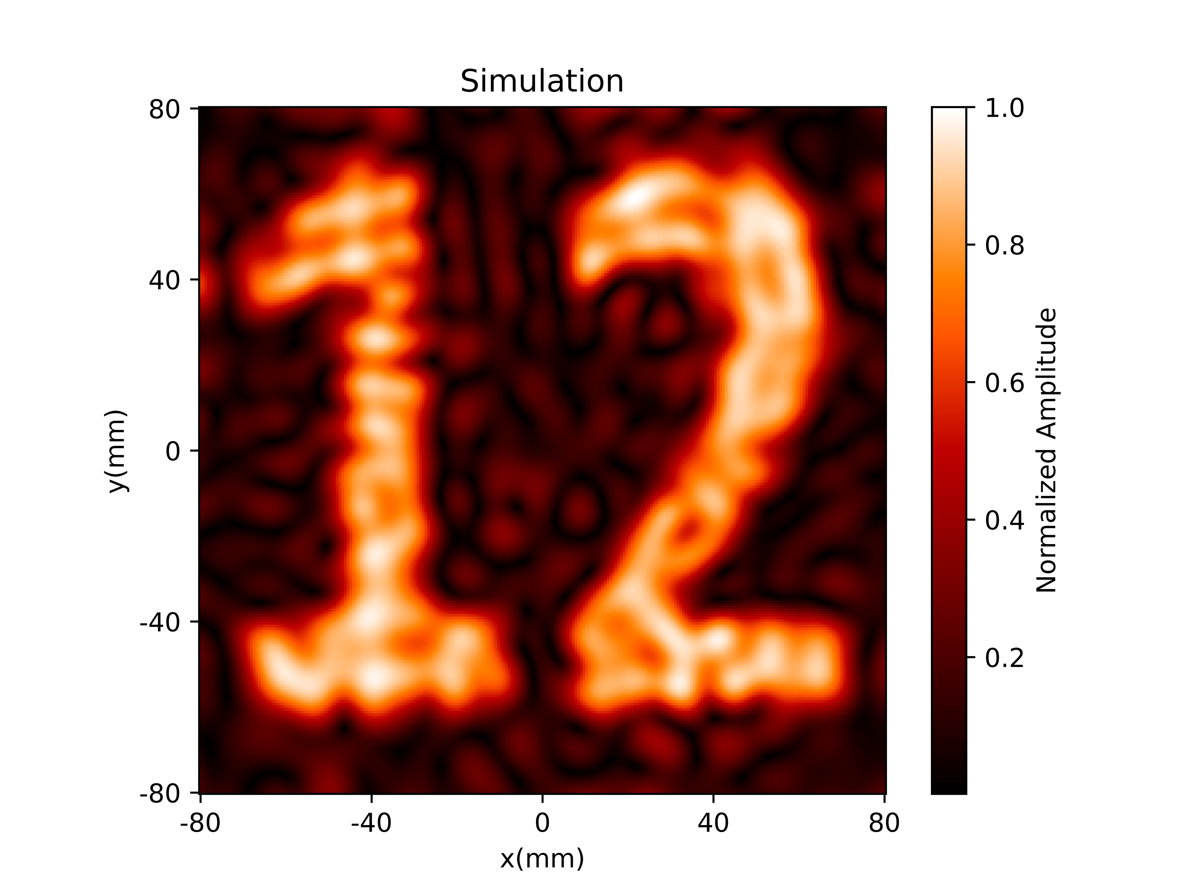
measurements/sim_12.png
