upnalab/usarrayheightmod/measurements/sim_A.png

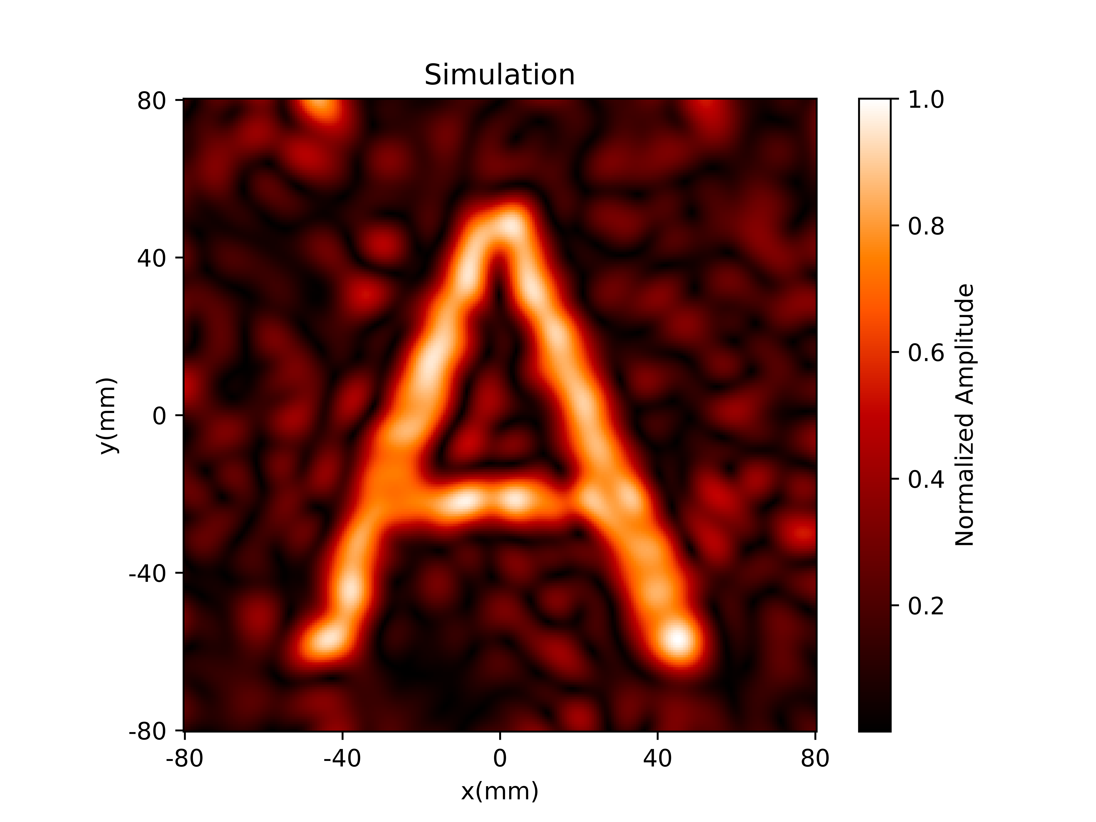
measurements/sim_A.png
