upnalab/usarrayheightmod/measurements/sim_star.png

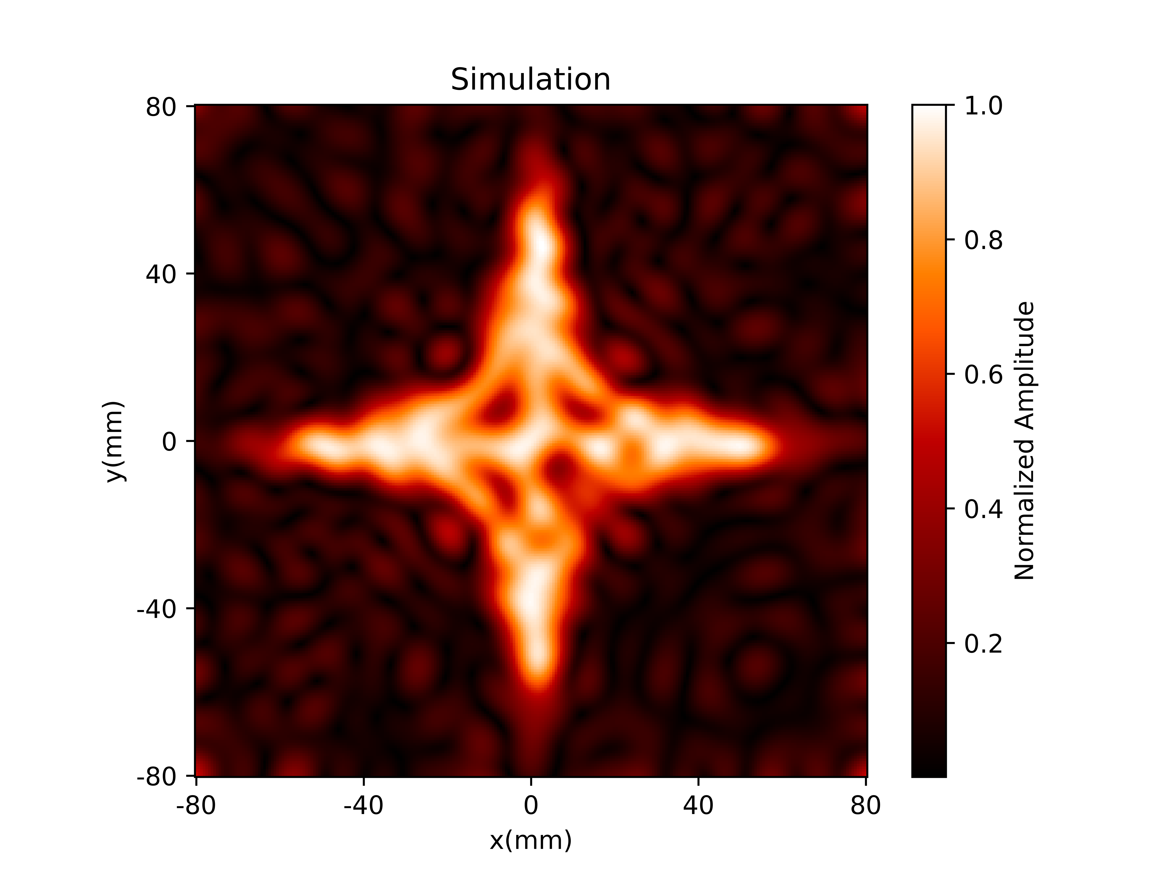
measurements/sim_star.png
