upnalab/usarrayheightmod/measurements/target_12.png

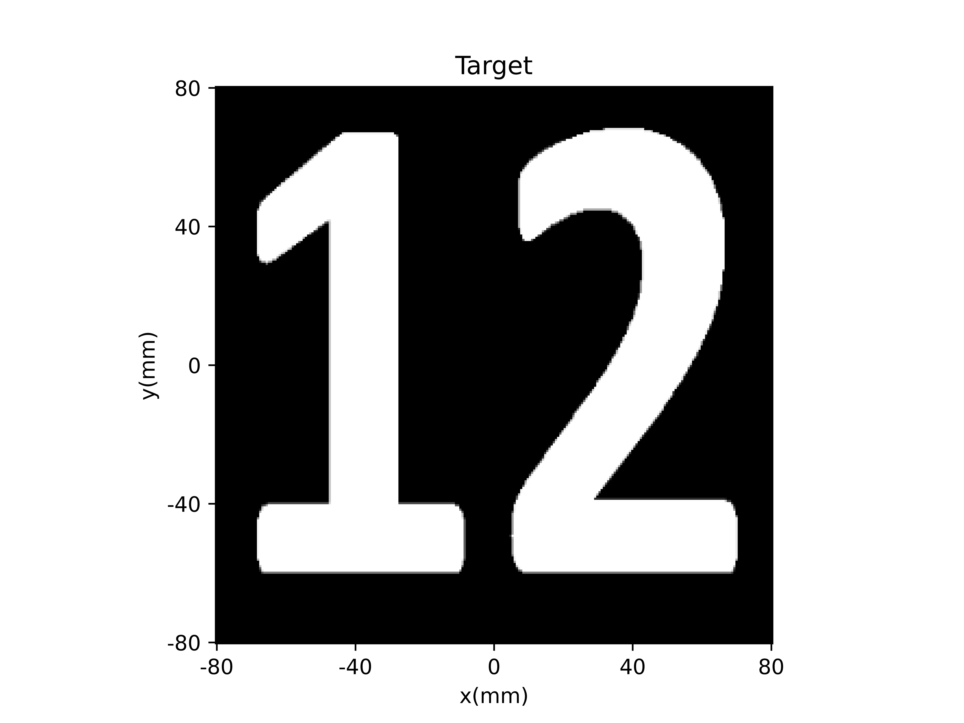
measurements/target_12.png
