upnalab/usarrayheightmod/measurements/target_A.png

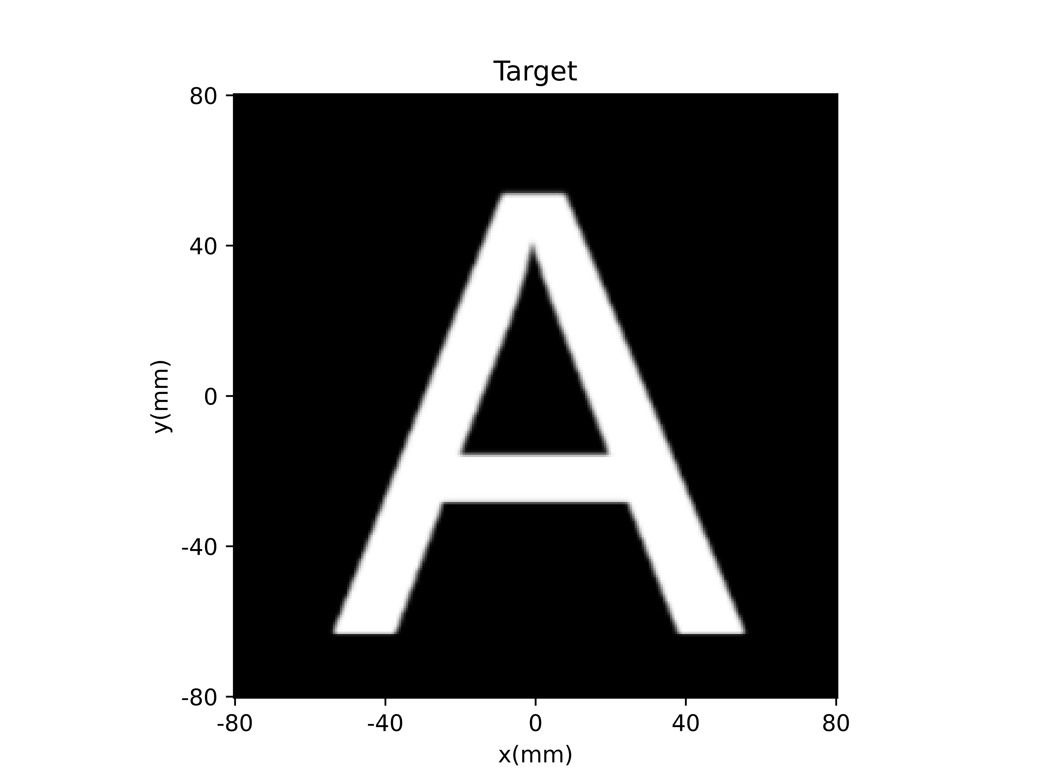
measurements/target_A.png
