upnalab/usarrayheightmod/measurements/target_star.png

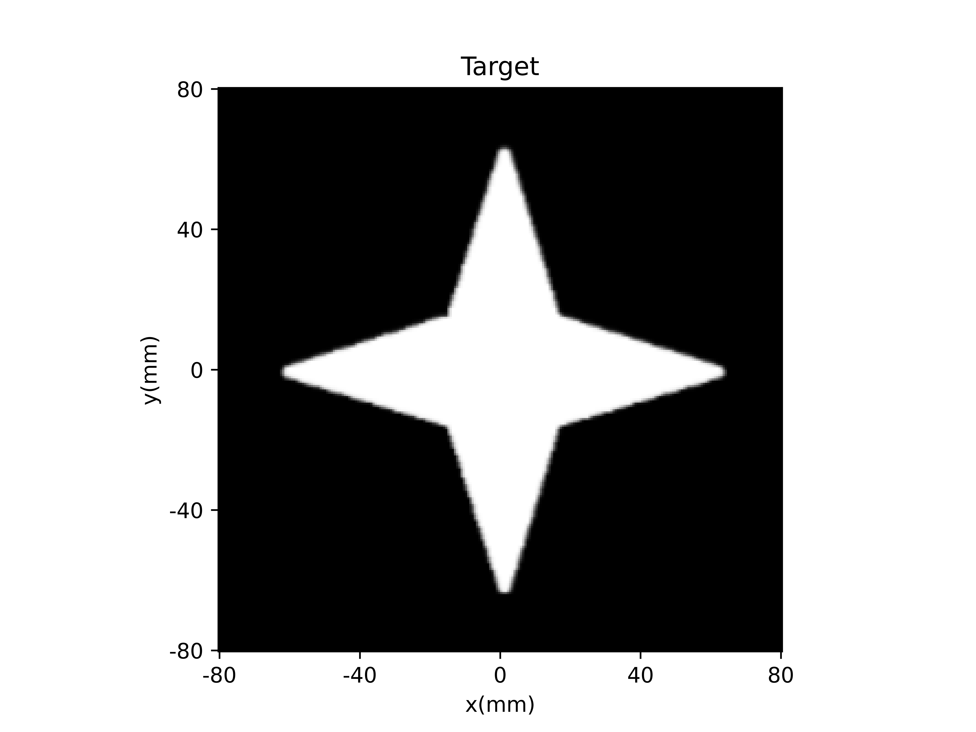
measurements/target_star.png
