upnalab/usarrayheightmod/results/Experiment_VS_Simulation_HeightMod_12.png

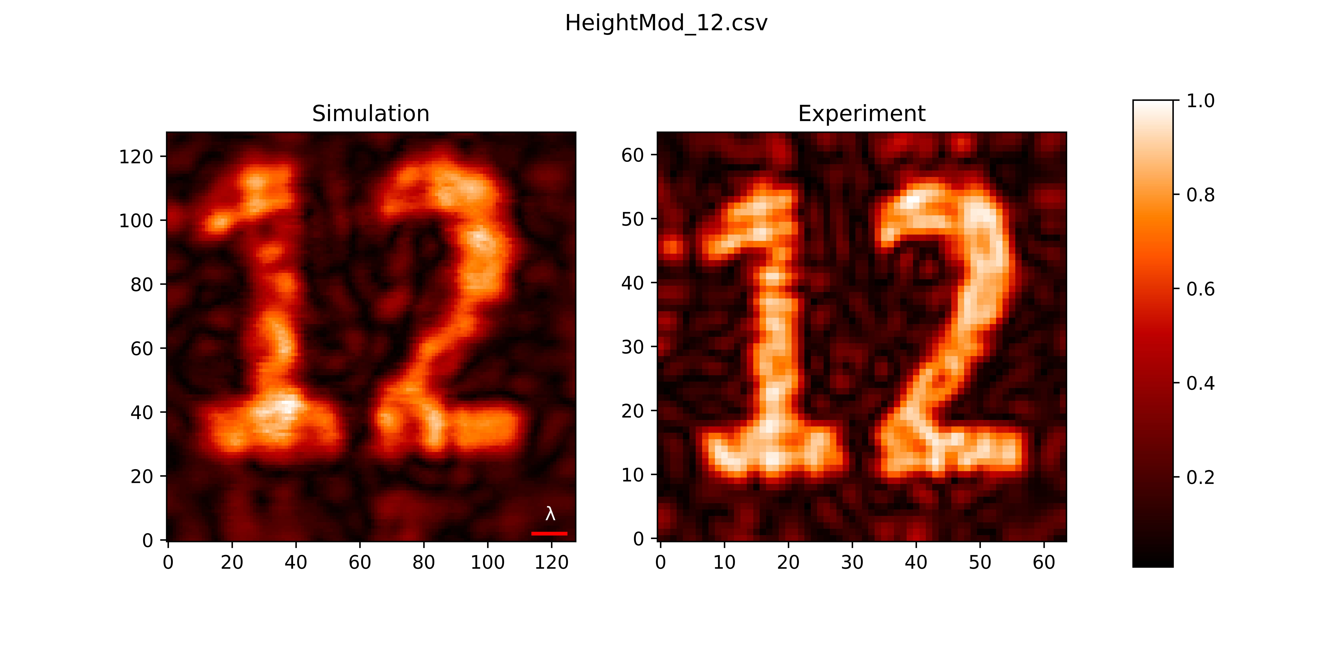
results/Experiment_VS_Simulation_HeightMod_12.png
