upnalab/usarrayheightmod/results/Experiment_VS_Simulation_HeightMod_A.png

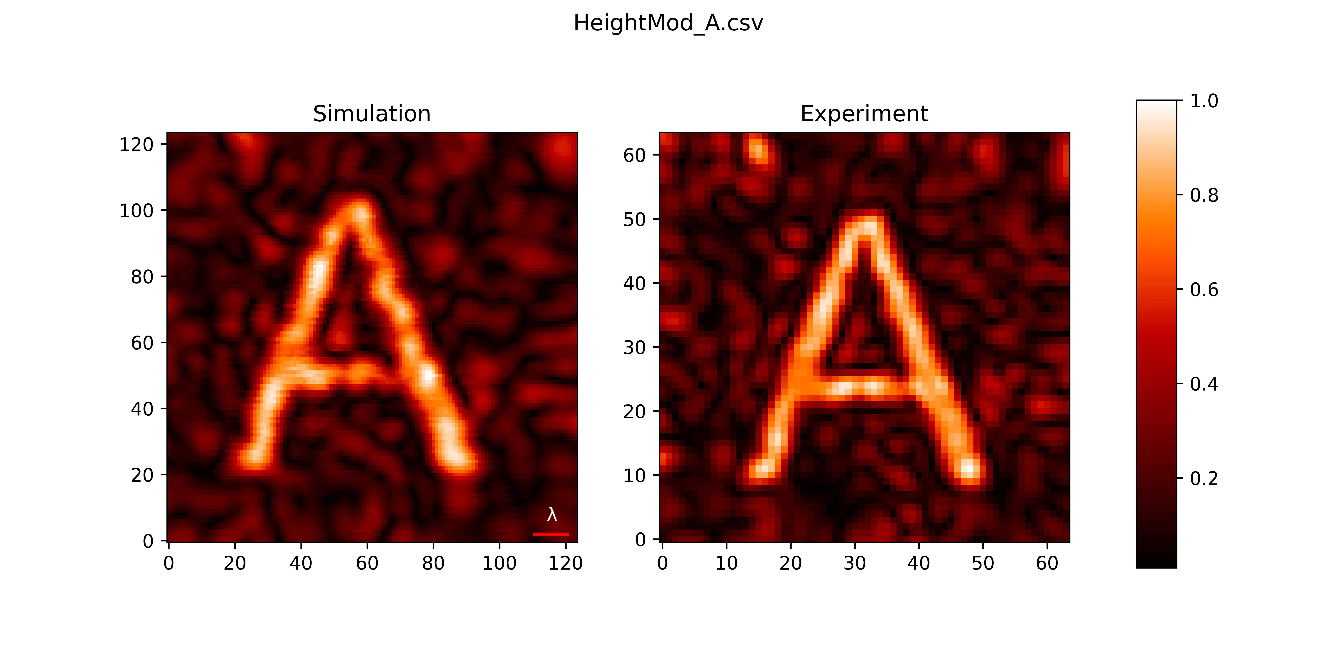
results/Experiment_VS_Simulation_HeightMod_A.png
